jmcpheron/picowallet/pcb/dossier/review/design-SHA256SUMS.txt

81872eb326079a7e8b5d7d5e1b19cf433eb0403c9ab9667d025cbc219fbe951f  design/B_Cu.gbr
2e30690aaf0712d75476c412137e2d9d4d11c8428289b69405e05833194e1649  design/B_Fab.gbr
f35687d87080b0f3686ef03e0c079b65ae2d905b86f3cc0620ea2f5d0d830985  design/B_Mask.gbr
2a0583e4f1f08f04dc978bb757d1210283100e4770bd0bd72f40201c464b8a35  design/B_Paste.gbr
18354fdda90aefe86f01dbc70a8d4ac4ed9822576b9fddc27e66ef9b916f4a84  design/B_SilkScreen.gbr
823afdf04d9c6c309ea86c9f785da4fdbc58092ca9bf7bde5bf54fca331086fa  design/Edge_Cuts.gbr
74883b58e809d55b0bc6244c77d480d6ff0cdf29ce8e10337ea52f4309ef3243  design/F_Cu.gbr
3864f394b6c3a682efa8f601bc7bfb813e6d987ae6614617fa555495596dba0d  design/F_Fab.gbr
b160e3052a8e661215c279790700f99fbb2ffc0b1814cabcb3420a72b8e14e5f  design/F_Mask.gbr
32e1bcf6dd70280c164ed8c9ef9c4a6f6ab28e5e05525b5f646602e4656c239d  design/F_Paste.gbr
fa26761cb678f5d729ef340bc35bac94bdb7481baf55dc918cb9726121abf4fc  design/F_SilkScreen.gbr
e51e13ea9f5cf1a3aba80c6a51722b144459b42f5522a788d916678455eaf316  design/atecc.py
47671b0118b700f60f467894f0017c4a4e2a5c7ac43126a3a6d44d783a9fd7d2  design/bom.csv
d2cc3fe4df4a8d1846834ca9a9e89f41f807217c7fe938fec09531b38b37acd0  design/circuit.json
2ee32a19055a602a06975289f33ecc65a3ce496ac5d460f3bfe1b75e12f026f0  design/drill-L1-L2.drl
3384cc93c1c2be9ab5b2f0fb1482502fd087c7b10cccd2463c61746d04682a67  design/drill_npth.drl
8be491ffda8b9145977cb7c0e572acd9fb334808aeca49469461d0e41f01ffbe  design/imports/AFC42_S12FMA_1H.tsx
1a8972742a19d952bdef4a81dbc08a3eb12bbb6a474e405c41814c8e8f9f5cf7  design/imports/ATECC608B_SSHDA_T.tsx
1c11bdfb14c2074dd8337bcc206597ea0cd844397efaa37cbe0326824e9cc2fb  design/imports/A_2N7002K.tsx
b427f95c3ecb185a983220215d4f819d88e12597ac880b04713199add4100ca5  design/imports/B2B_PH_K_S_LF__SN_.tsx
0096762589c44025e8de1cc9b50725c5d652869b592f98cea48bb7ed34450979  design/imports/B8B_PH_K_S_LF__SN_.tsx
e7616fea44cbe588cf2a56cc619590fded075c63ccea7ce70d8436919f30bb55  design/imports/FPC_05FB_12PH20.tsx
7e6e95e033e55d2333b14894a894e1f6c5e5995f0d5044a608a69153240c5a7e  design/imports/HS20HS072RX.tsx
20b32934aec5f2864cbb48cf8da05da7b60f25d9f67b9723107a9162c68af262  design/imports/KH_6X6X5H_STM.tsx
8308a2bd2d0942416d6335a00306846be59e4fa2a5d607b795276ab017445468  design/imports/MCP2221A_I_ST.tsx
dc7c8d19167b896671e425b0ab83c15ee2b98f2e8f7ee3580d204d0af8f0a4de  design/imports/MSK12C02.tsx
080d922cc619edd11ae2b99730031f0dcc4e410ed6c89468a13a04f0ba893a95  design/imports/N114_2413THBIG01_H13.tsx
d8937ad016772eebd5f3176e59195f99bb56accab89966493c41f63082c26c04  design/imports/Raspberry_Pi_Pico_2W.tsx
e574e61f85b4c484d38929691d93fe90a69a7a41fd3f569a63147b37680dcbe7  design/imports/SKRHABE010.tsx
5de4d8bbd46f4217eb1491d092df8b797234da56ba7755f28d0653d1a24292b8  design/imports/SS14.tsx
67e55c82c61c12562ab0b4fbd8571564f8616f0f8f78ff265328f881599fb617  design/imports/TP4056.tsx
c4853684f1a7005c34f4000c8a4169bb6ec0265d493bd5304ac0a39d371ed727  design/imports/TYPE_C_24P_GTJB_040.tsx
a82b10c8e38ad41f17fd554e613dbc87036179dead6d384e9041da5c413de141  design/imports/TYPE_C_31_G_06.tsx
01b787781f85690d2ee1d6bc622a94667b03a3ae0d313eb4d7b8245be5163ab8  design/index.circuit.tsx
dd3722d458c4e9695f280ac042d3c78b1068ff26b8c834af29469a27c2366ffa  design/kicad-project.zip
5e905d84e344de93d0ba6c1a8fc089d557e6350b650668da4855b38a73cc6c2c  design/lcd.py
f00cfa05f2660cc76b7d9e6f8d97057246a0fbf60b70eb4c4683b0e3c232fc22  design/pick_and_place.csv
