jmcpheron/picowallet/pcb/dossier/NETLIST-v0.8.md

# Generated v0.8 netlist

Positions are compiled footprint centers, in mm. PCB rotations are not supplier CPL rotations.

| Part | X | Y | Side | PCB rotation |
|---|---:|---:|---|---:|
| U1 | -12.9400 | 0.0000 | bottom | 180 |
| DISP1 | 2.0000 | 0.0000 | top | 0 |
| J3 | -6.2500 | -0.4300 | top | 270 |
| C4 | -10.0000 | -6.0000 | top | 0 |
| R6 | 4.0000 | -20.5000 | top | 0 |
| Q1 | 10.0000 | -20.3000 | top | 0 |
| R7 | 9.0000 | -16.5000 | top | 0 |
| SW5 | -33.0000 | 0.0001 | top | 45 |
| SW1 | 34.0000 | 8.0000 | top | 90 |
| SW2 | 34.0000 | -6.0000 | top | 90 |
| U2 | -33.0000 | 15.0000 | top | 0 |
| R1 | -27.0000 | 19.0000 | top | 0 |
| R2 | -27.0000 | 11.0000 | top | 0 |
| C1 | -27.0000 | 15.0000 | top | 0 |
| BT1 | 28.0000 | 2.0000 | bottom | 0 |
| J2 | 28.0000 | 20.0000 | bottom | 0 |
| C2 | 24.0000 | -16.0000 | top | 0 |
| U3 | 30.0000 | -17.5000 | top | 0 |
| R3 | 35.5000 | -17.5000 | top | 90 |
| C3 | 24.0000 | -20.5000 | top | 0 |
| D1 | 18.0000 | -20.5000 | top | 0 |
| SW6 | -30.0000 | -19.2940 | top | 0 |
| SJ1 | 39.0000 | -10.0000 | top | 0 |
| R10 | 37.5000 | -14.0000 | top | 0 |
| Q2 | 18.0000 | -16.0000 | top | 0 |
| R8 | 13.0000 | -16.0000 | top | 0 |
| R9 | -23.0000 | -16.0000 | top | 0 |
| LED1 | -20.0000 | -20.0000 | top | 180 |
| R4 | -16.0000 | -20.0000 | top | 0 |
| LED2 | -8.0000 | -20.0000 | top | 180 |
| R5 | -4.0000 | -20.0000 | top | 0 |

## Connections

- unnamed / unconnected: U1.1
- unnamed / unconnected: U1.2
- GND: U1.3, U1.38, J3.1, J3.12, C4.2, Q1.2, R7.2, SW5.5, SW1.2, SW2.2, U2.4, C1.2, J2.2, C2.2, U3.1, U3.3, U3.9, R3.2, C3.2, SW6.3, R10.2, LED1.1
- unnamed / unconnected: U1.4, SW5.1
- unnamed / unconnected: U1.5, SW5.2
- SDA: U1.6, U2.5, R1.1
- SCL: U1.7, U2.6, R2.1
- unnamed / unconnected: U1.8
- unnamed / unconnected: U1.9
- unnamed / unconnected: U1.10
- unnamed / unconnected: U1.11, J3.3
- unnamed / unconnected: U1.12, J3.2
- unnamed / unconnected: U1.13
- unnamed / unconnected: U1.14, J3.4
- unnamed / unconnected: U1.15, J3.5
- unnamed / unconnected: U1.16, J3.6
- unnamed / unconnected: U1.17, Q1.1, R7.1
- unnamed / unconnected: U1.18
- unnamed / unconnected: U1.19
- unnamed / unconnected: U1.20, SW1.1
- unnamed / unconnected: U1.21, SW5.3
- unnamed / unconnected: U1.22, SW2.1
- unnamed / unconnected: U1.23
- unnamed / unconnected: U1.24, SW5.6
- unnamed / unconnected: U1.25
- unnamed / unconnected: U1.26, SW5.4
- unnamed / unconnected: U1.27
- unnamed / unconnected: U1.28
- unnamed / unconnected: U1.29
- unnamed / unconnected: U1.30
- unnamed / unconnected: U1.31
- unnamed / unconnected: U1.32
- unnamed / unconnected: U1.33
- unnamed / unconnected: U1.34
- unnamed / unconnected: U1.35
- V3_3: U1.36, J3.8, J3.9, C4.1, U2.8, R1.2, R2.2, C1.1, R4.1
- unnamed / unconnected: U1.37
- VSYS: U1.39, R6.1, D1.1
- VBUS: U1.40, C2.1, U3.4, SJ1.1, R5.1
- unnamed / unconnected: U1.41
- unnamed / unconnected: U1.42
- unnamed / unconnected: U1.43
- unnamed / unconnected: U1.44
- unnamed / unconnected: U1.45
- unnamed / unconnected: U1.46
- unnamed / unconnected: DISP1.1
- unnamed / unconnected: J3.7
- unnamed / unconnected: J3.10, R6.2
- unnamed / unconnected: J3.11, Q1.3
- unnamed / unconnected: J3.13
- unnamed / unconnected: J3.14
- unnamed / unconnected: SW5.7
- unnamed / unconnected: SW5.8
- unnamed / unconnected: SW1.3
- unnamed / unconnected: SW1.4
- unnamed / unconnected: SW2.3
- unnamed / unconnected: SW2.4
- unnamed / unconnected: U2.1
- unnamed / unconnected: U2.2
- unnamed / unconnected: U2.3
- unnamed / unconnected: U2.7
- unnamed / unconnected: BT1.1
- BAT: J2.1, U3.5, C3.1, SW6.1, Q2.2, R8.1
- unnamed / unconnected: U3.2, R3.1
- unnamed / unconnected: U3.6
- unnamed / unconnected: U3.7, LED2.2
- unnamed / unconnected: U3.8, SJ1.2, R10.1
- unnamed / unconnected: D1.2, Q2.3
- unnamed / unconnected: SW6.2, R9.1
- unnamed / unconnected: SW6.4
- unnamed / unconnected: SW6.5
- unnamed / unconnected: SW6.6
- unnamed / unconnected: SW6.7
- unnamed / unconnected: Q2.1, R8.2, R9.2
- unnamed / unconnected: LED1.2, R4.2
- unnamed / unconnected: LED2.1, R5.2

## J3 pads

| Pin | X | Y |
|---|---:|---:|
| 1 | -5.0000 | 2.3200 |
| 2 | -5.0000 | 1.8200 |
| 3 | -5.0000 | 1.3200 |
| 4 | -5.0000 | 0.8200 |
| 5 | -5.0000 | 0.3200 |
| 6 | -5.0000 | -0.1800 |
| 7 | -5.0000 | -0.6800 |
| 8 | -5.0000 | -1.1800 |
| 9 | -5.0000 | -1.6800 |
| 10 | -5.0000 | -2.1800 |
| 11 | -5.0000 | -2.6800 |
| 12 | -5.0000 | -3.1800 |
| 13 | -7.5000 | -4.1800 |
| 14 | -7.5000 | 3.3200 |
