jmcpheron/picowallet/art/bar_screen.png

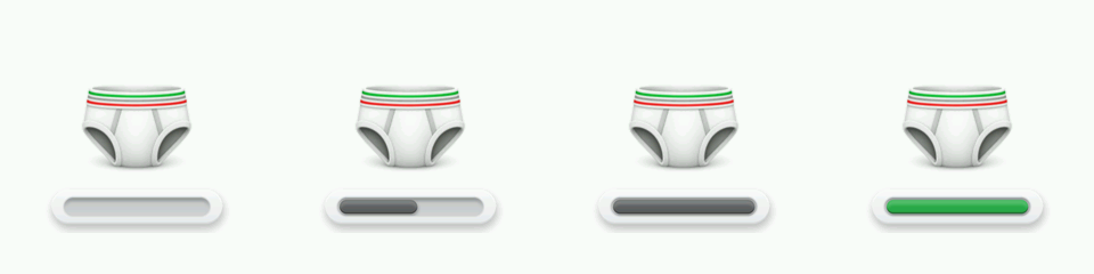
art/bar_screen.png
