jmcpheron/picowallet/case/zez0000/base_v5_qr_bottom.png

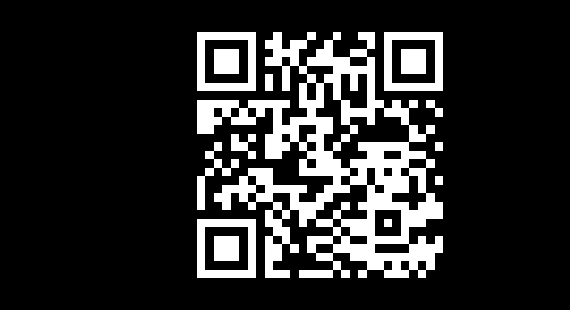
case/zez0000/base_v5_qr_bottom.png
