jmcpheron/picowallet/g3.png

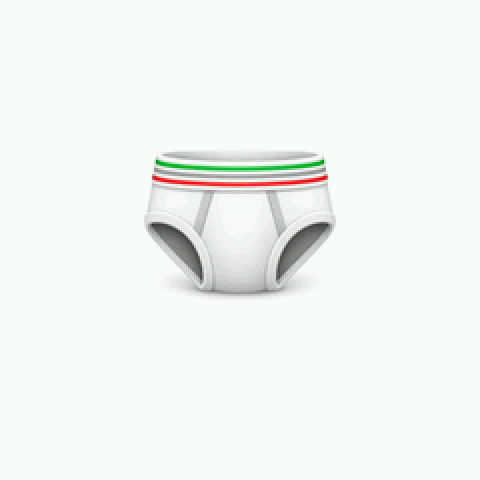
g3.png
