jmcpheron/picowallet/pcb/dossier/datasheets/panel-page-01.png

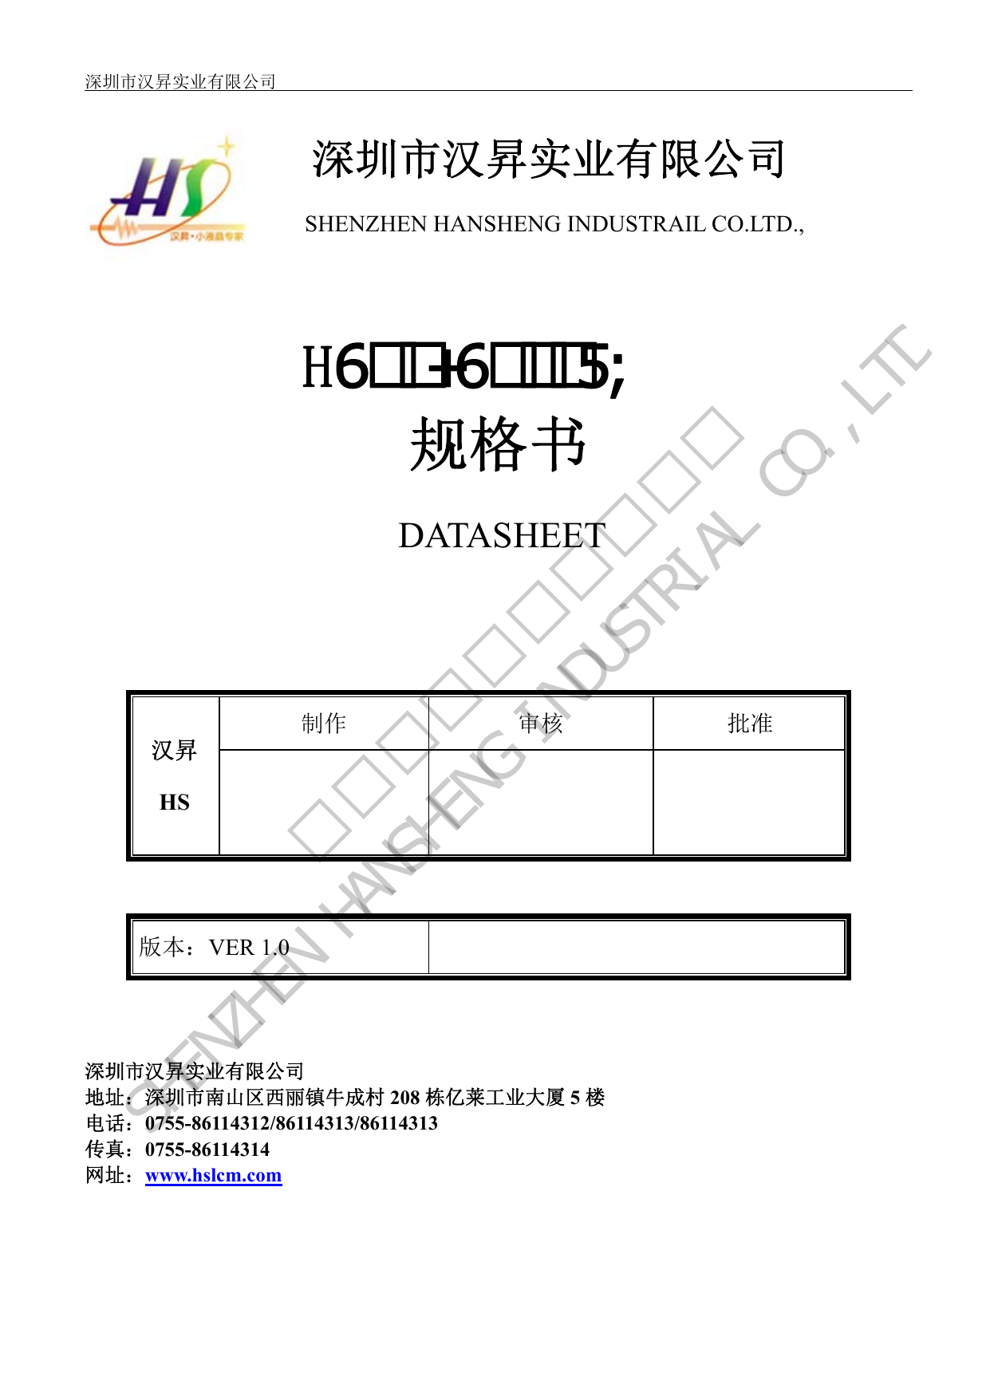
pcb/dossier/datasheets/panel-page-01.png
