jmcpheron/picowallet/pcb/dossier/datasheets/panel-page-02.png

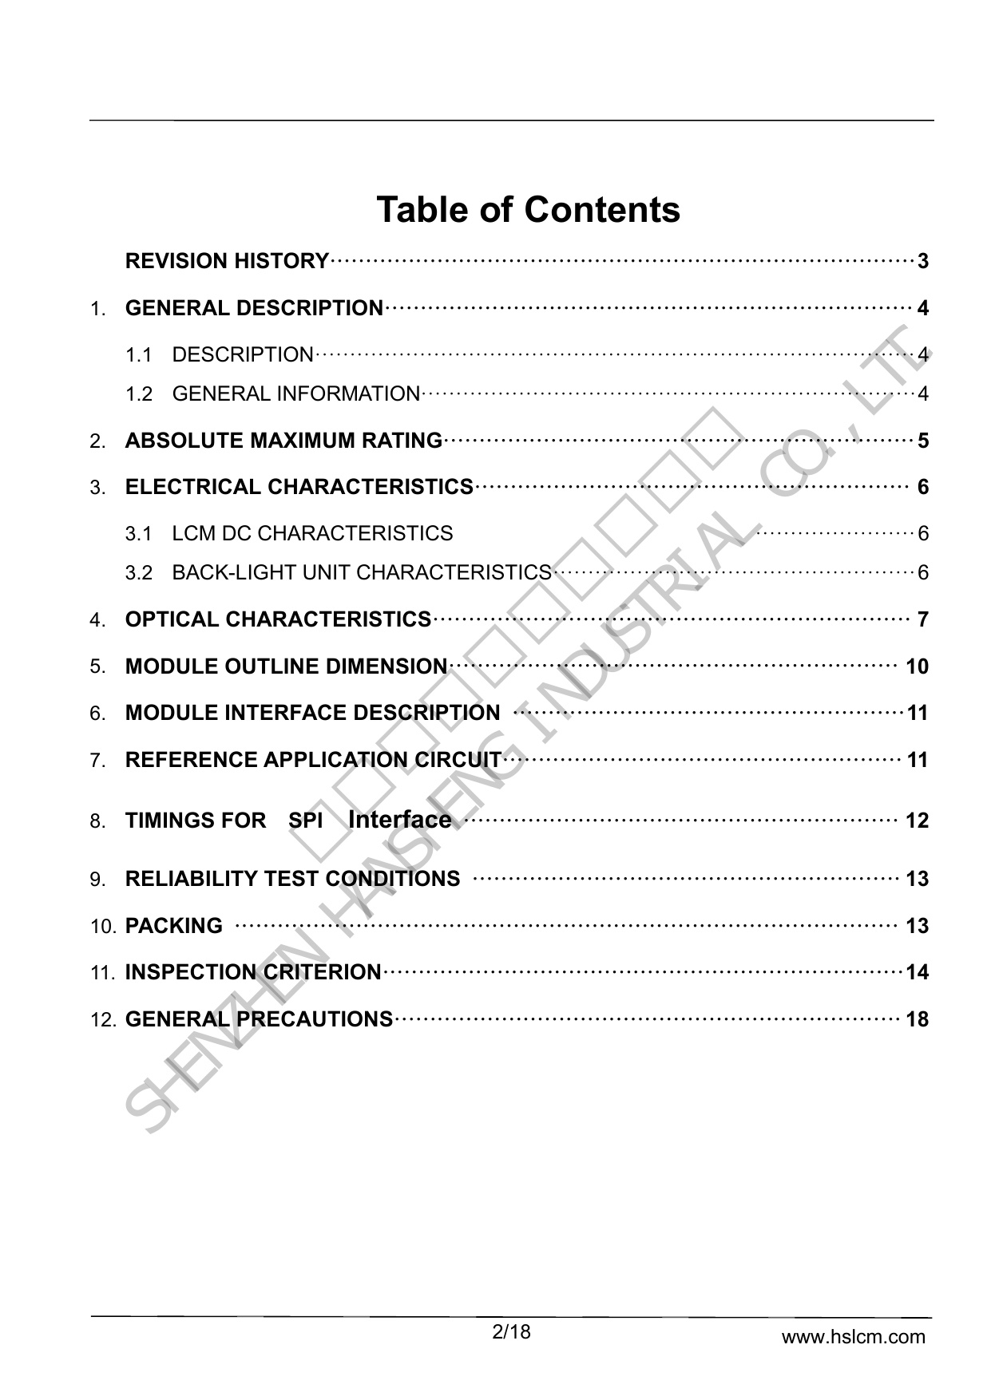
pcb/dossier/datasheets/panel-page-02.png
