jmcpheron/picowallet/pcb/dossier/datasheets/panel-page-03.png

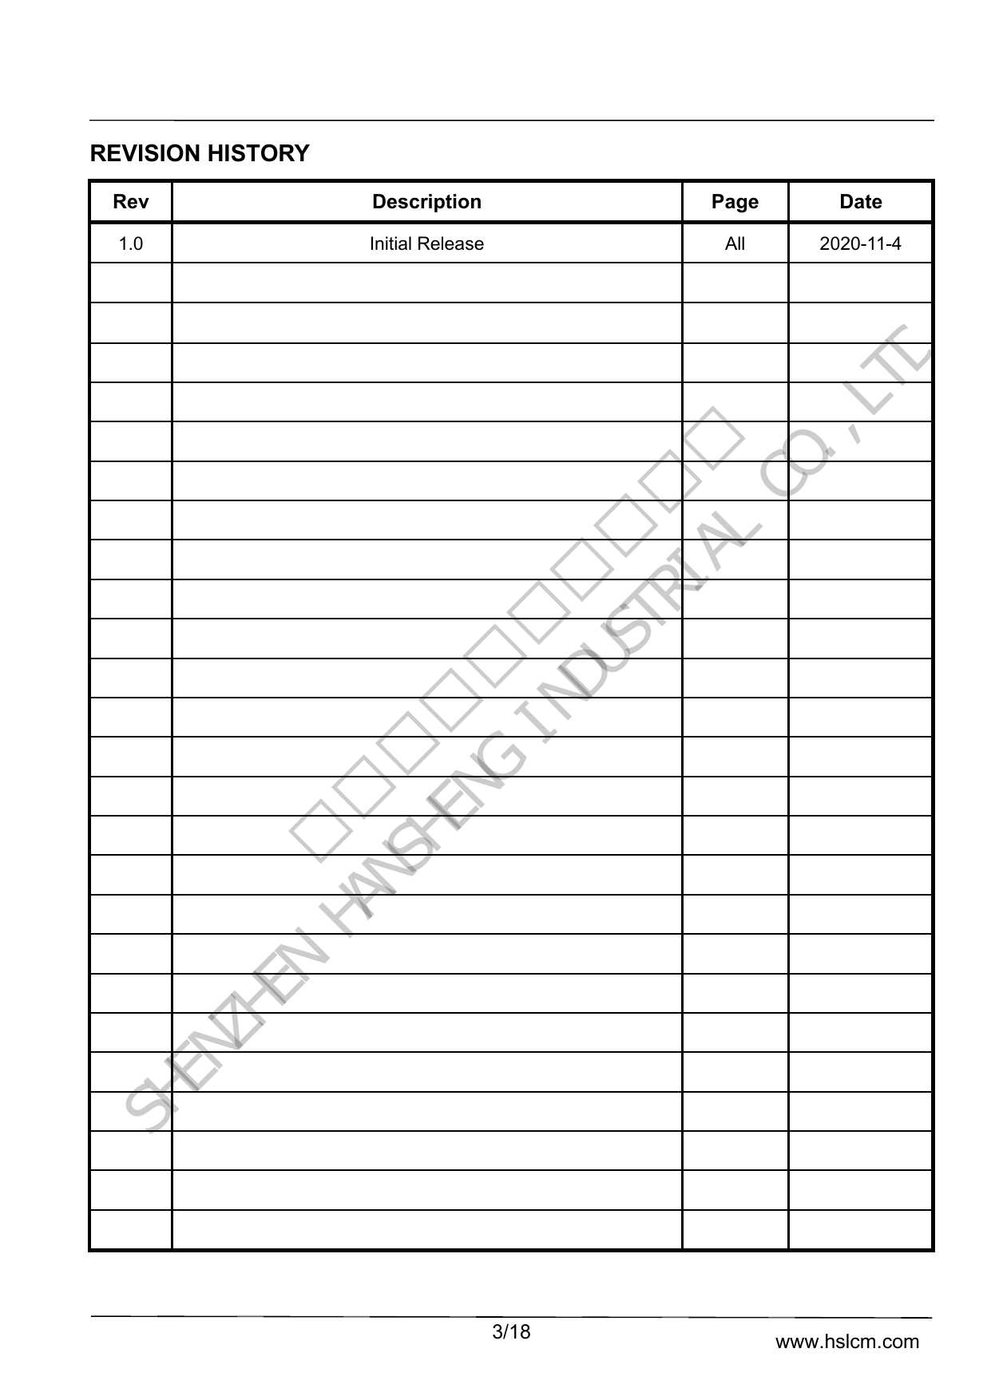
pcb/dossier/datasheets/panel-page-03.png
