jmcpheron/picowallet/pcb/dossier/datasheets/panel-page-04.png

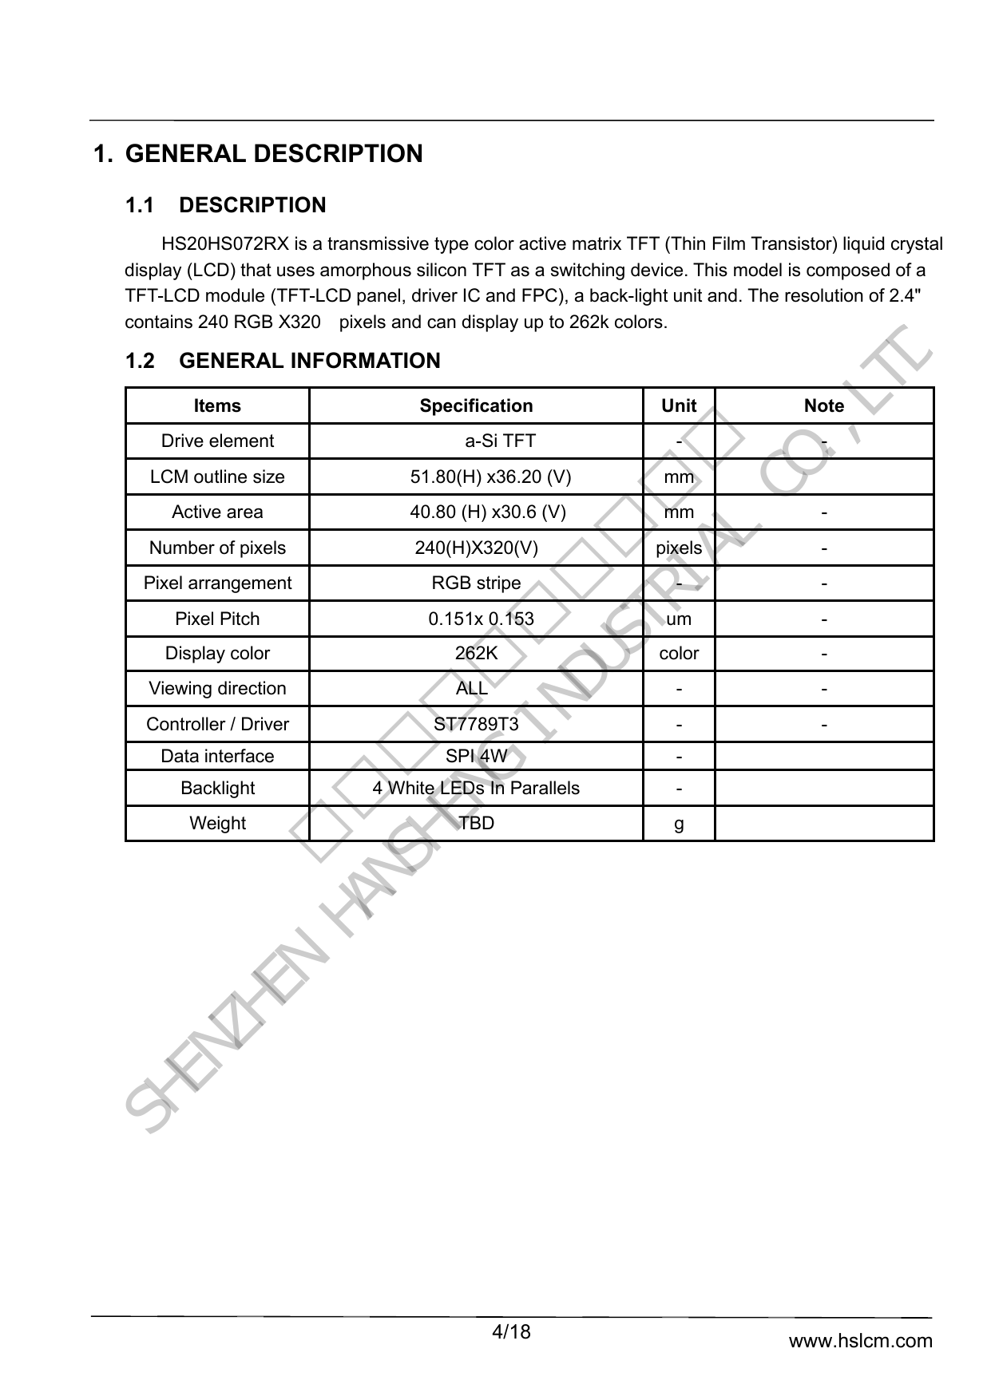
pcb/dossier/datasheets/panel-page-04.png
