jmcpheron/picowallet/pcb/dossier/datasheets/panel-page-05.png

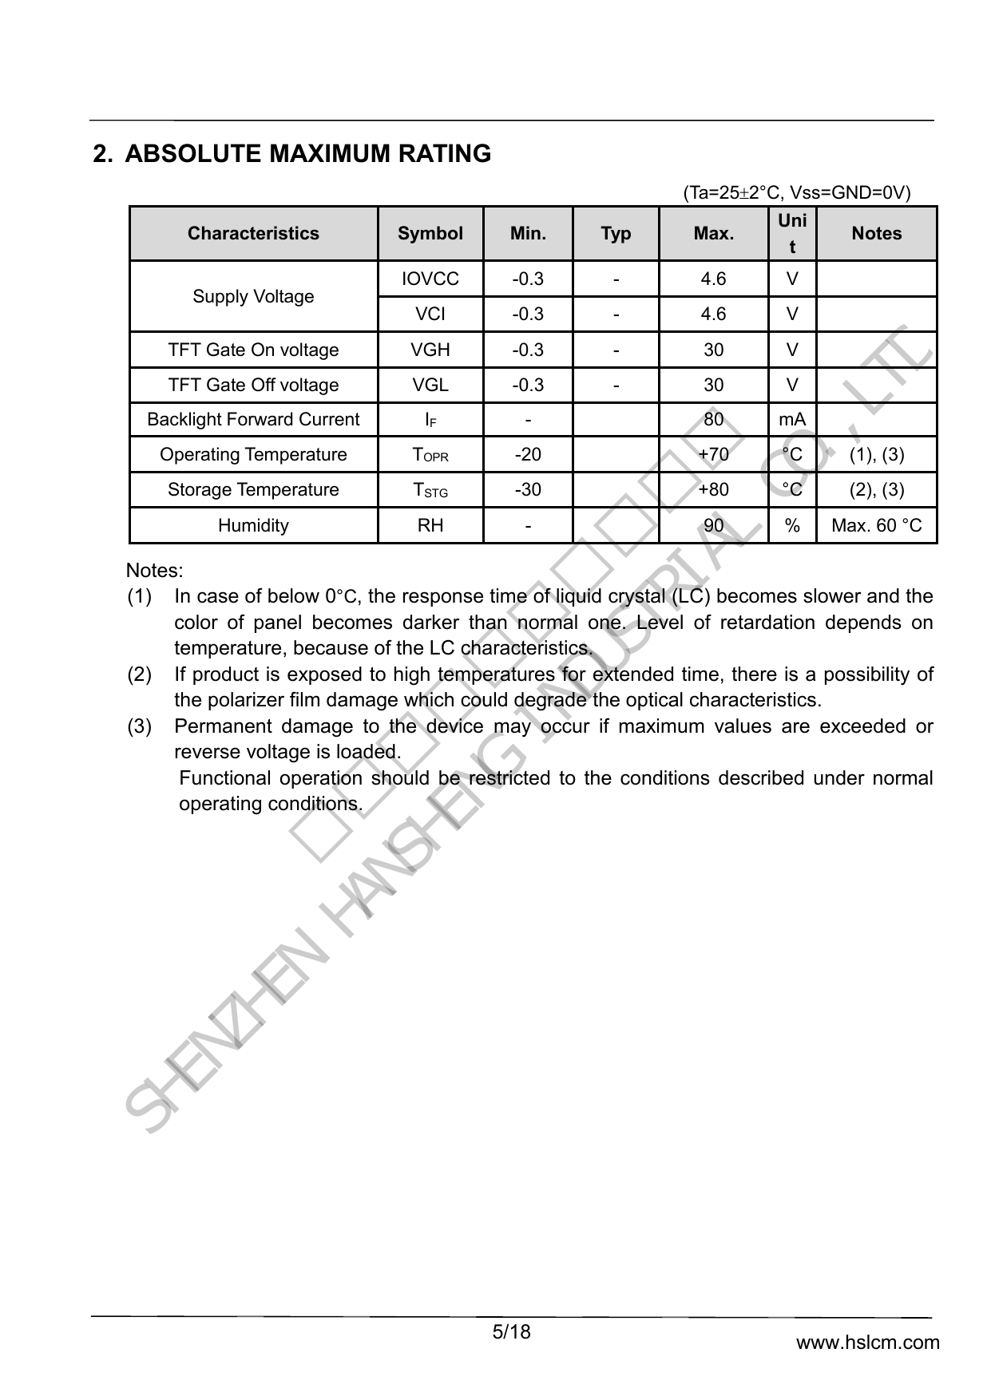
pcb/dossier/datasheets/panel-page-05.png
