jmcpheron/picowallet/pcb/dossier/datasheets/panel-page-06.png

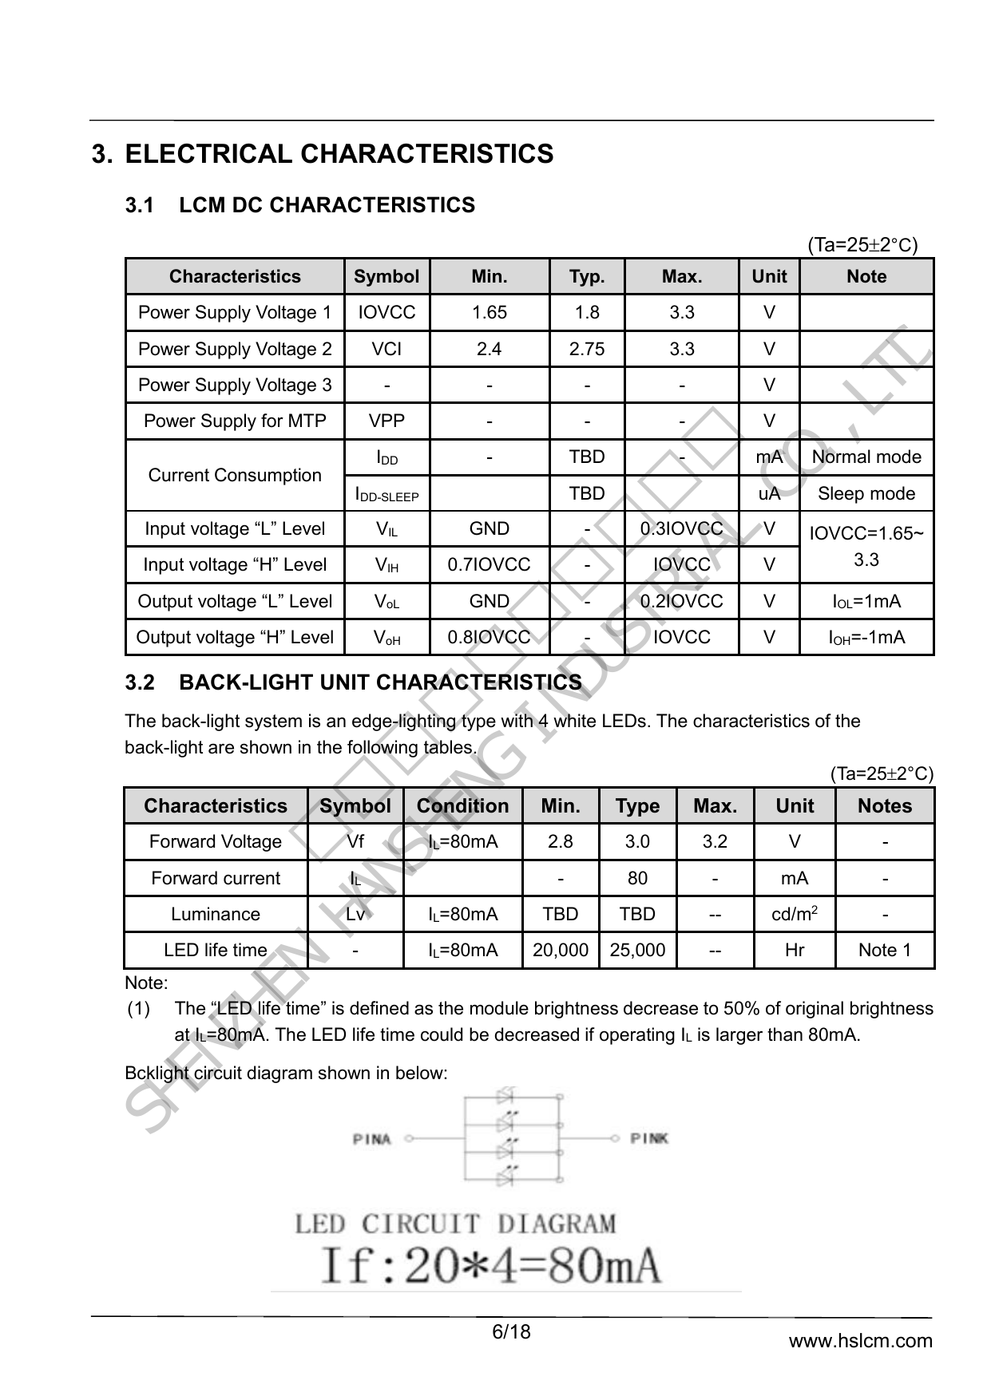
pcb/dossier/datasheets/panel-page-06.png
