jmcpheron/picowallet/pcb/dossier/datasheets/panel-page-07.png

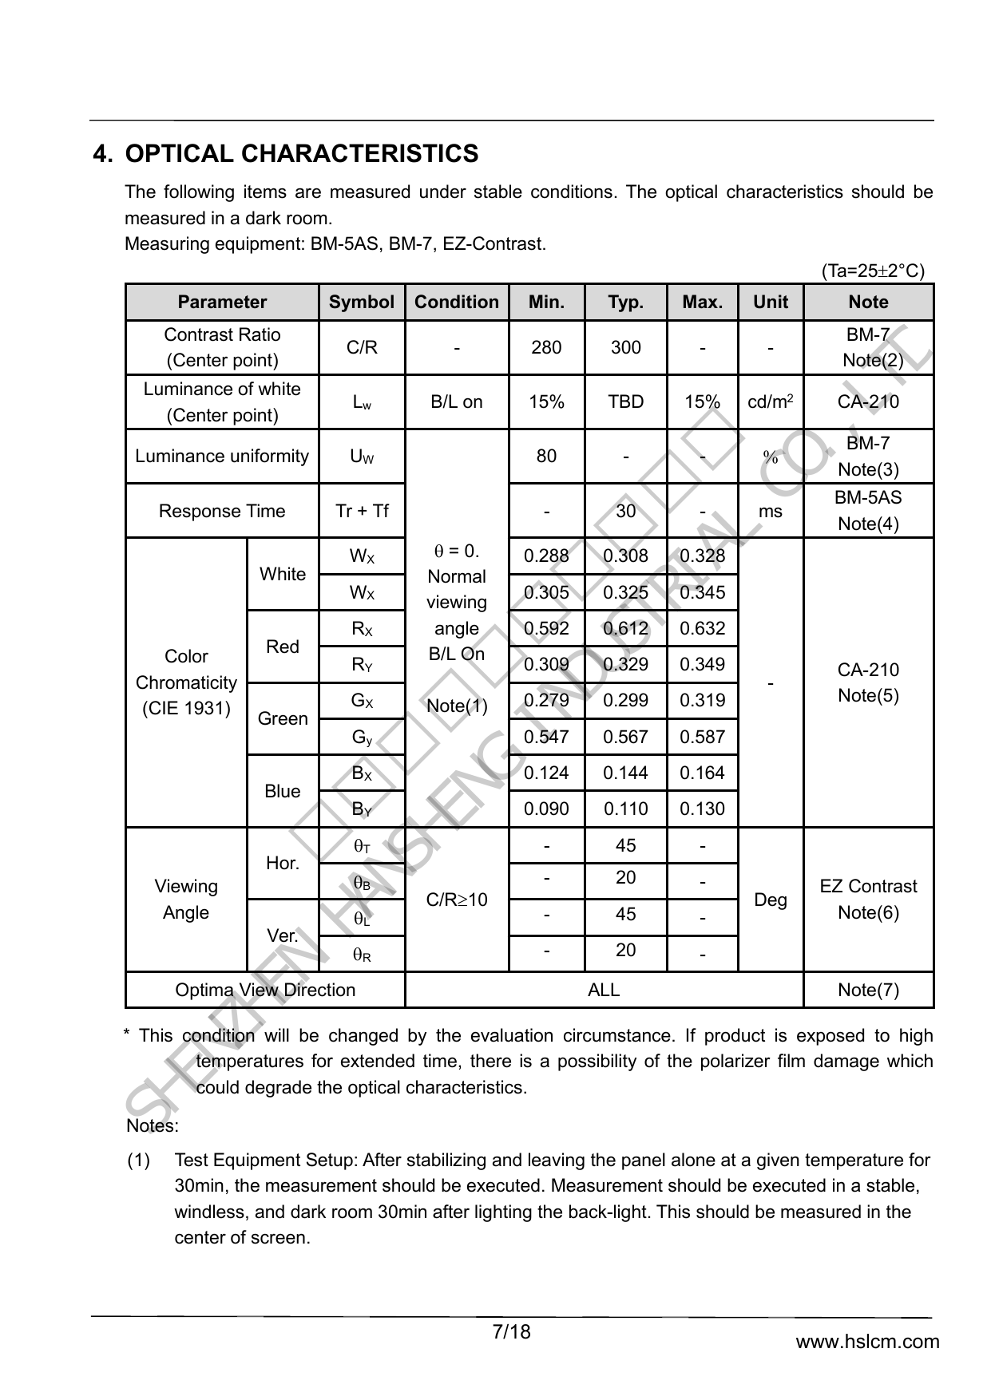
pcb/dossier/datasheets/panel-page-07.png
