jmcpheron/picowallet/pcb/dossier/datasheets/panel-page-08.png

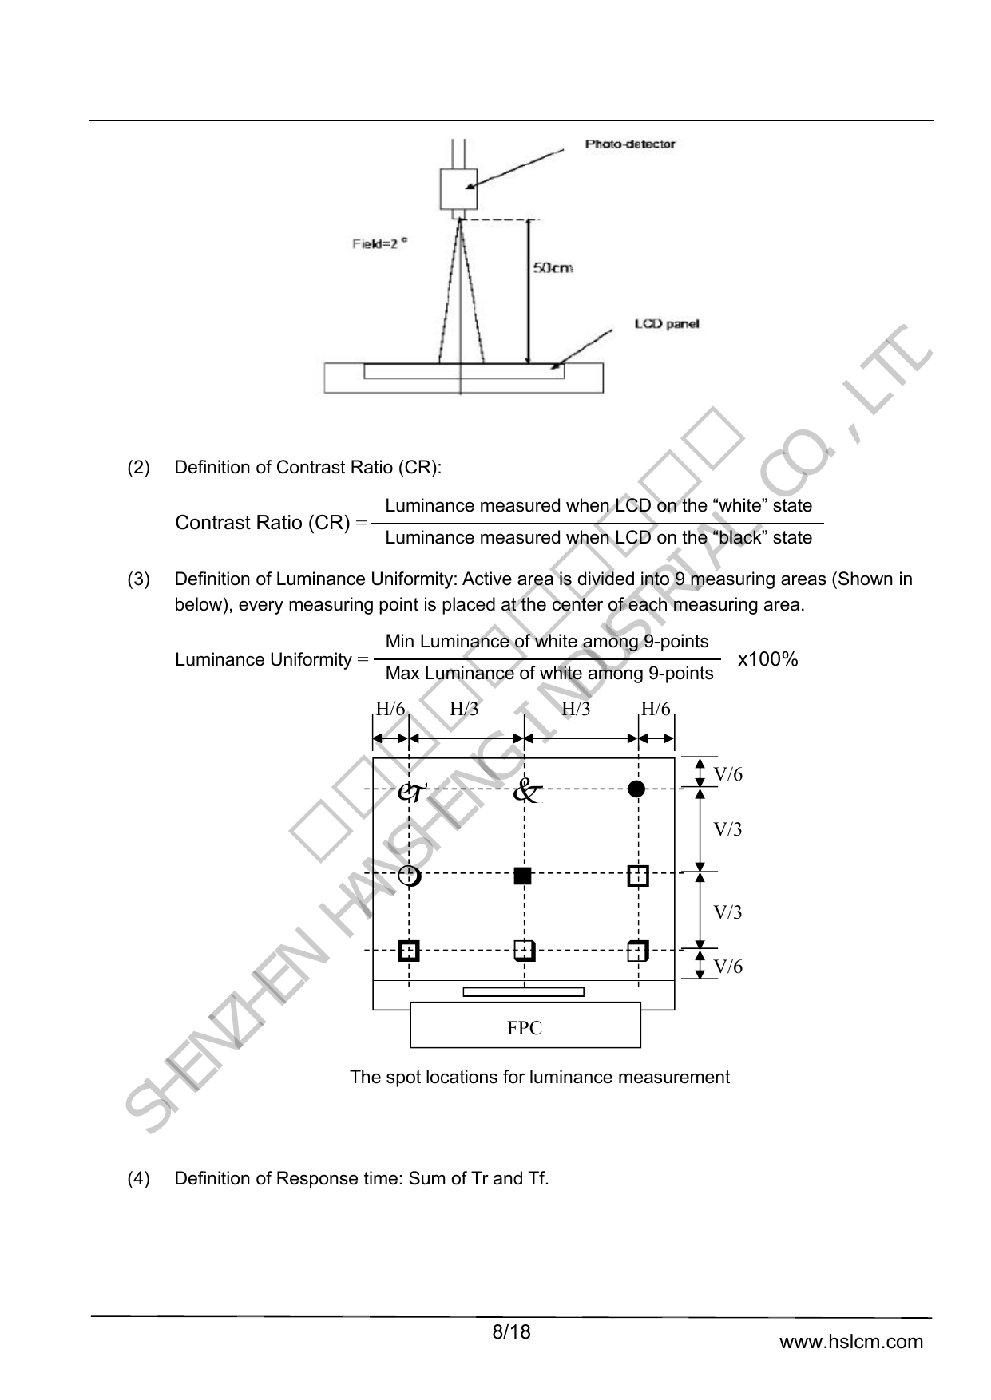
pcb/dossier/datasheets/panel-page-08.png
