jmcpheron/picowallet/pcb/dossier/datasheets/panel-page-09.png

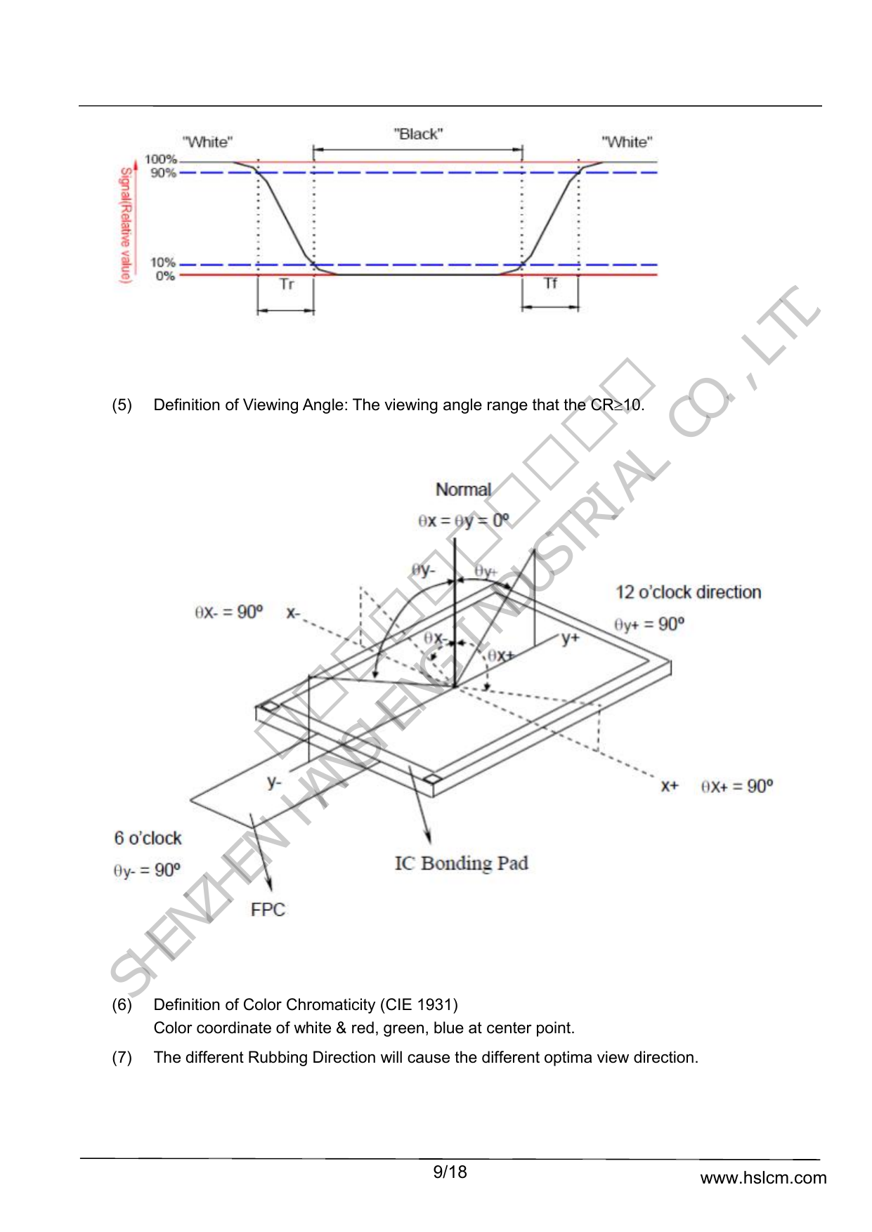
pcb/dossier/datasheets/panel-page-09.png
