jmcpheron/picowallet/pcb/dossier/datasheets/panel-page-10.png

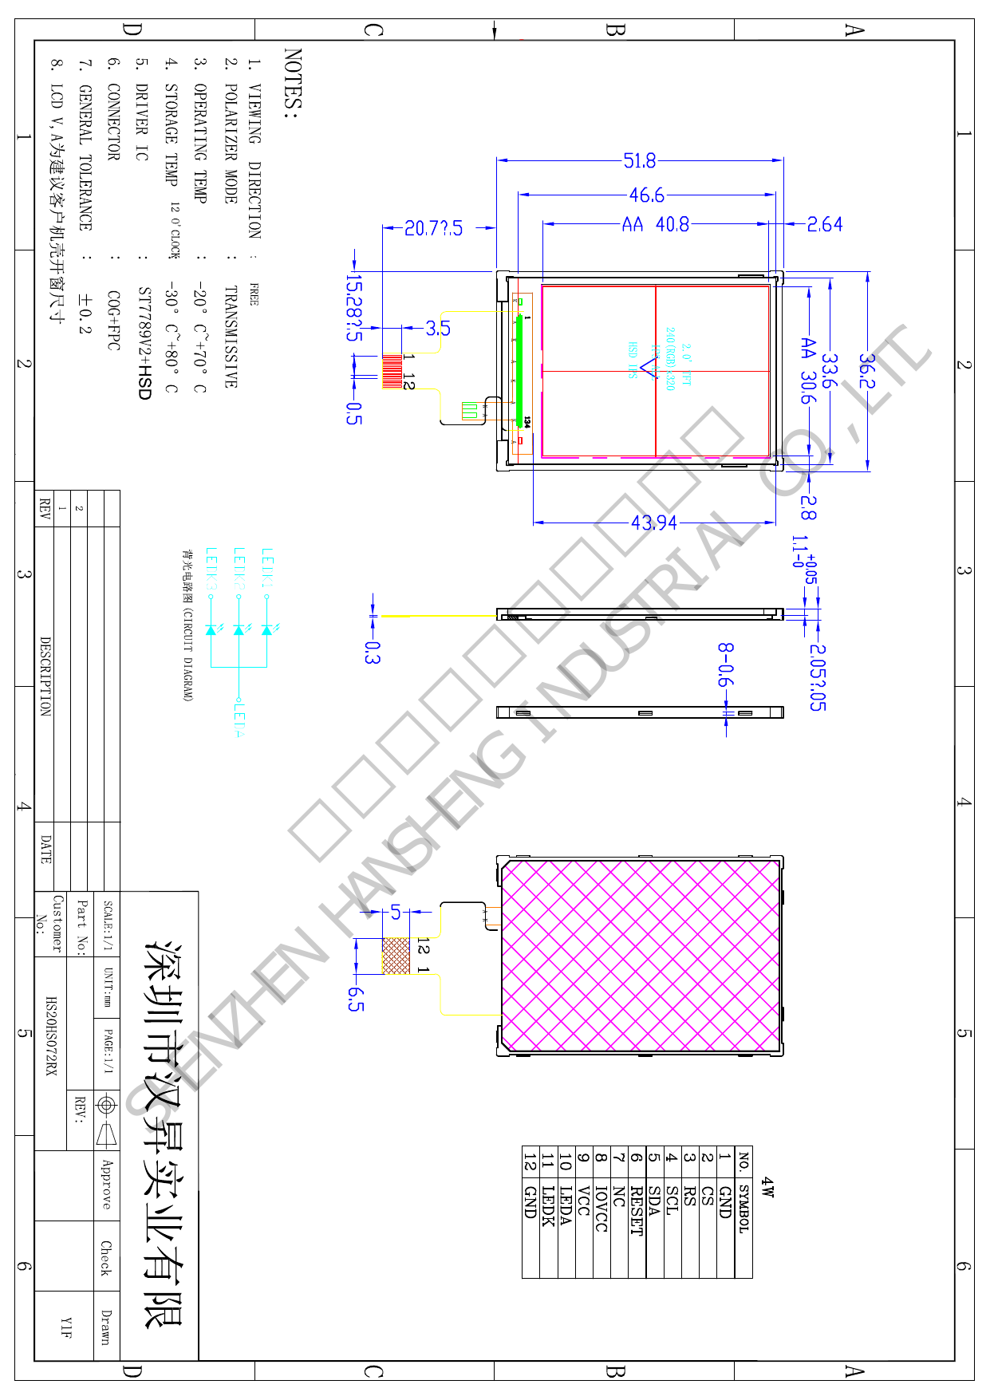
pcb/dossier/datasheets/panel-page-10.png
