jmcpheron/picowallet/pcb/dossier/datasheets/panel-page-11.png

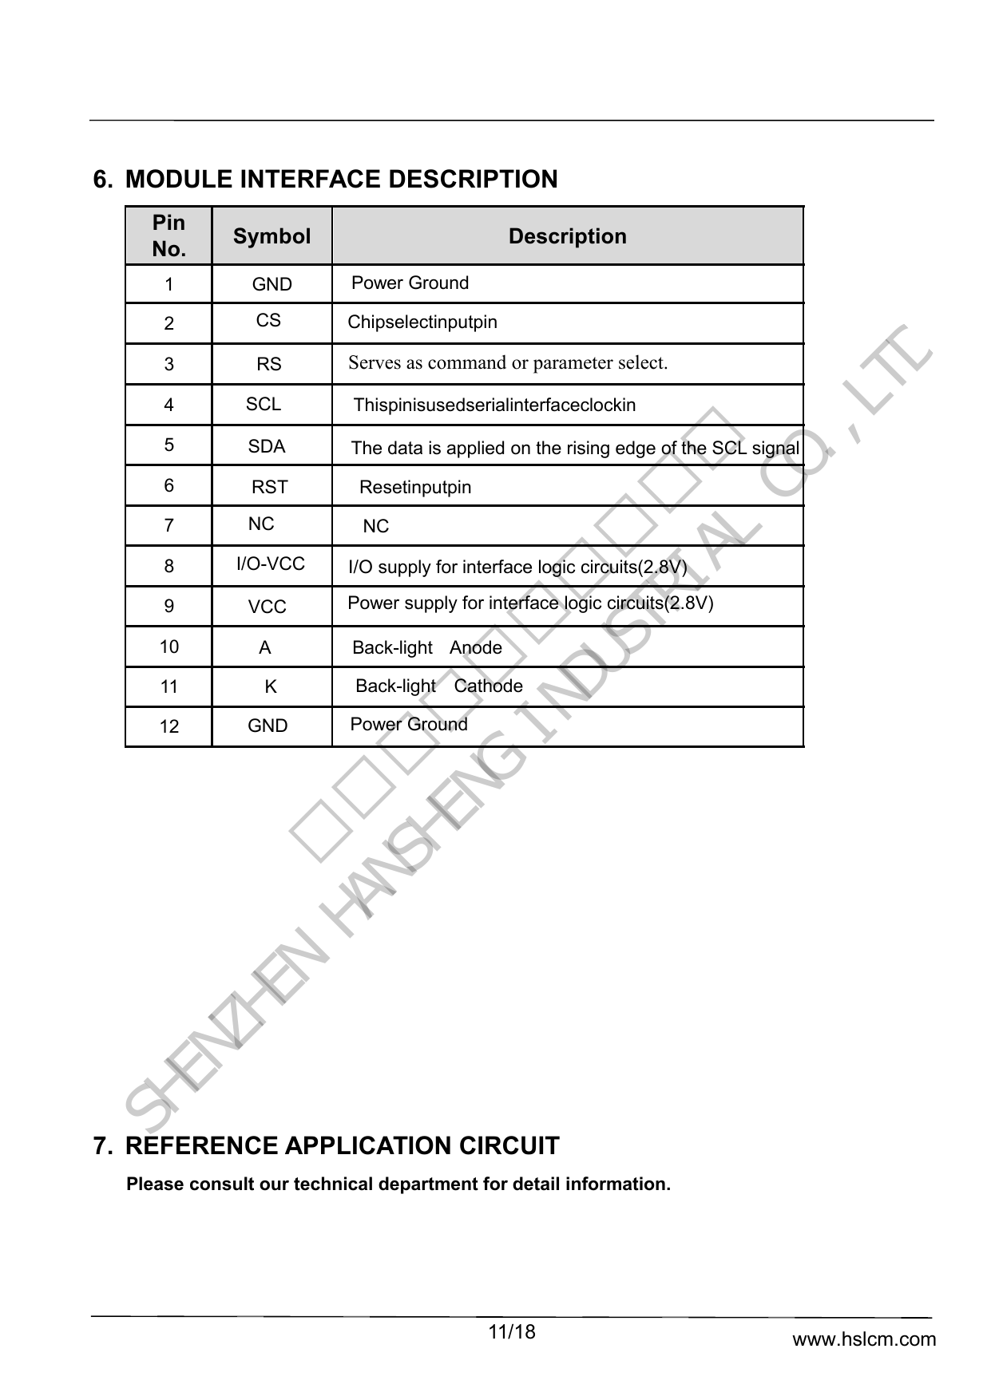
pcb/dossier/datasheets/panel-page-11.png
