jmcpheron/picowallet/pcb/dossier/datasheets/panel-page-12.png

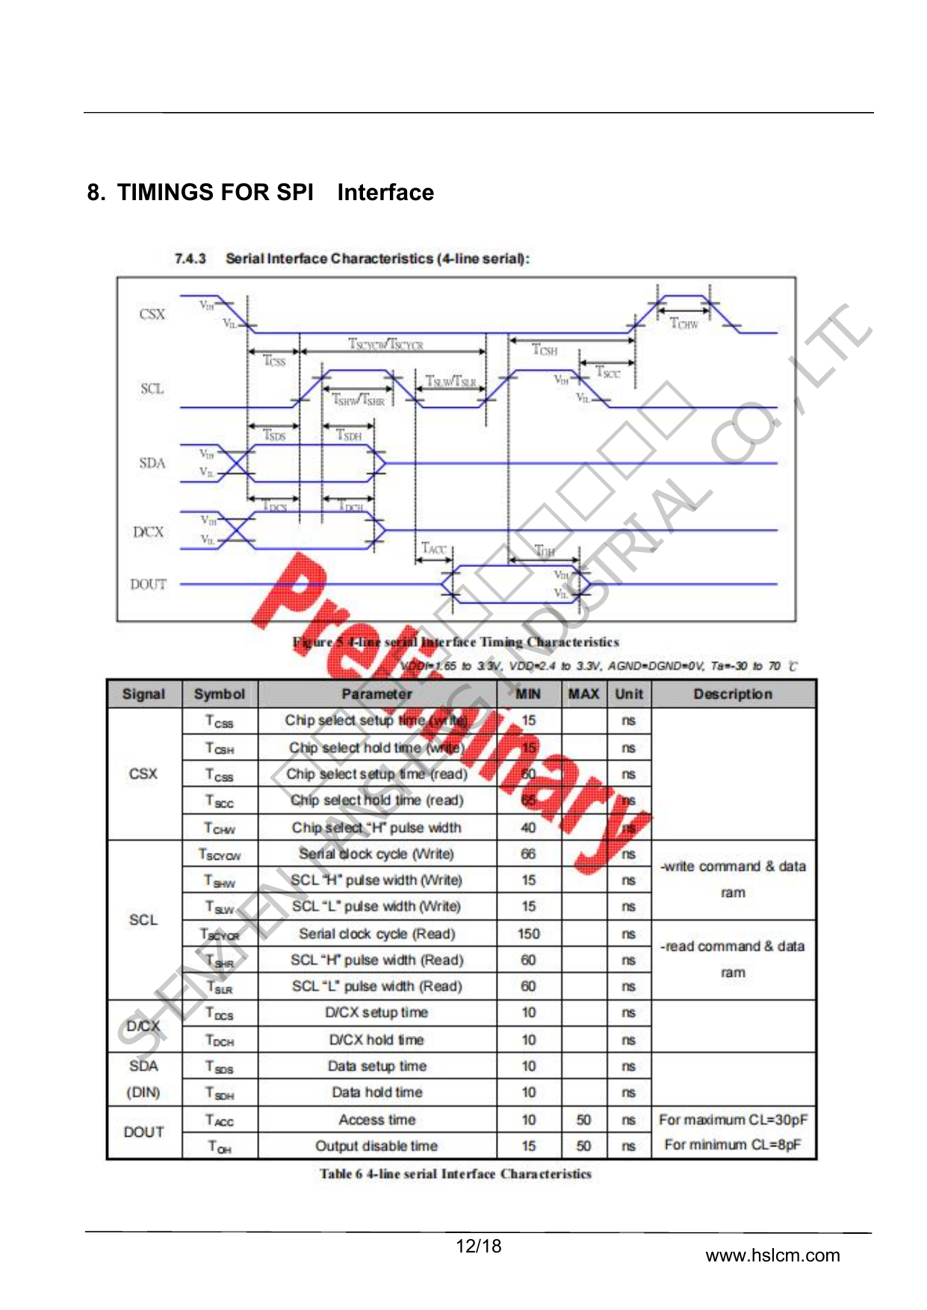
pcb/dossier/datasheets/panel-page-12.png
