jmcpheron/picowallet/pcb/dossier/datasheets/panel-page-13.png

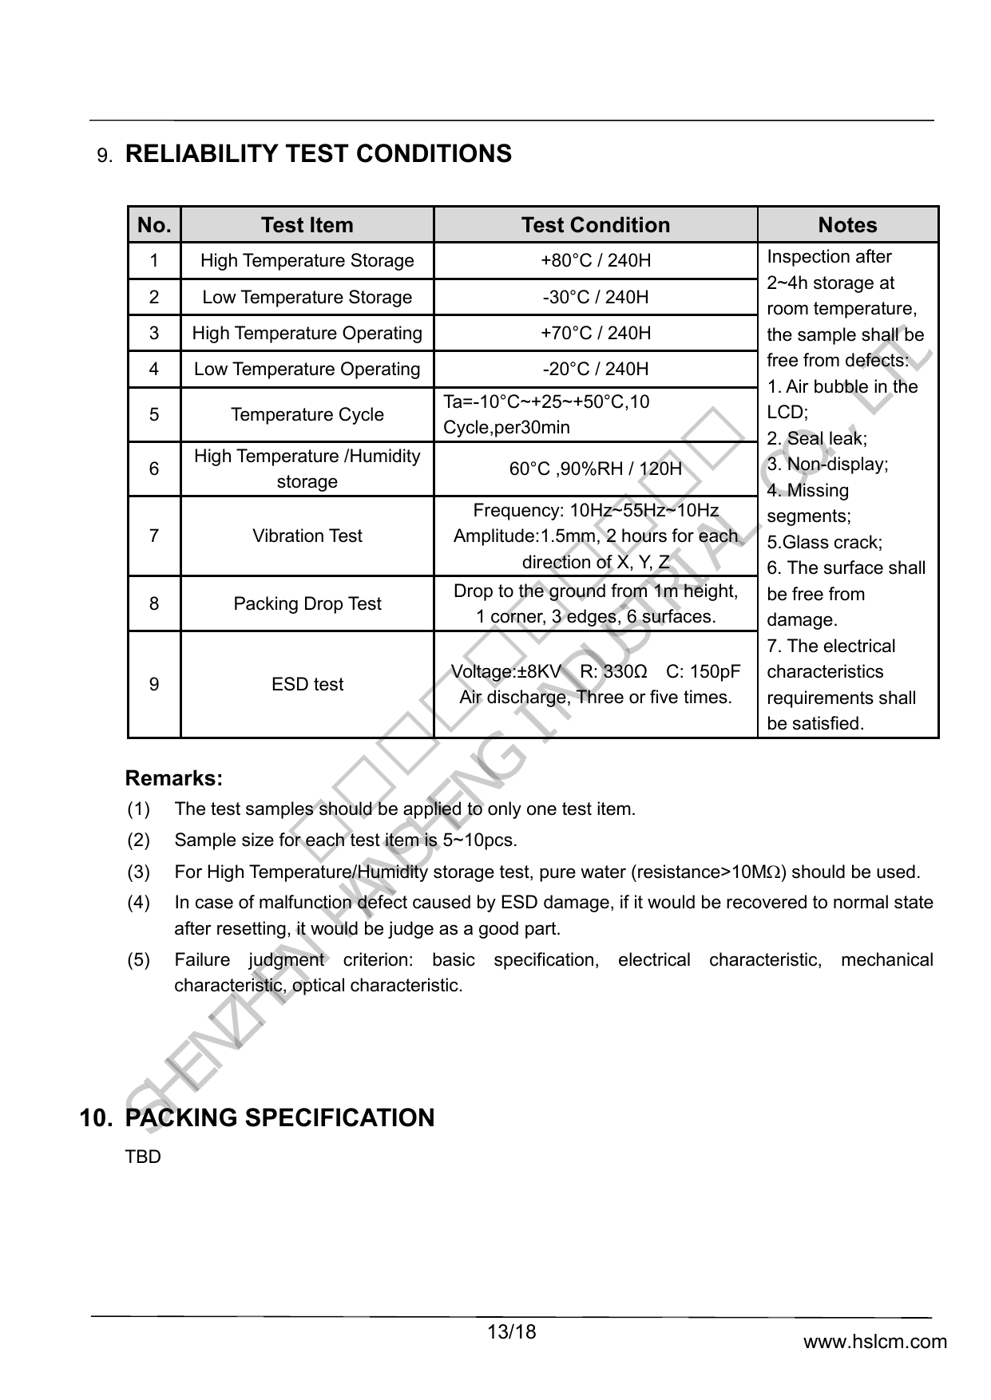
pcb/dossier/datasheets/panel-page-13.png
