jmcpheron/picowallet/pcb/dossier/datasheets/panel-page-14.png

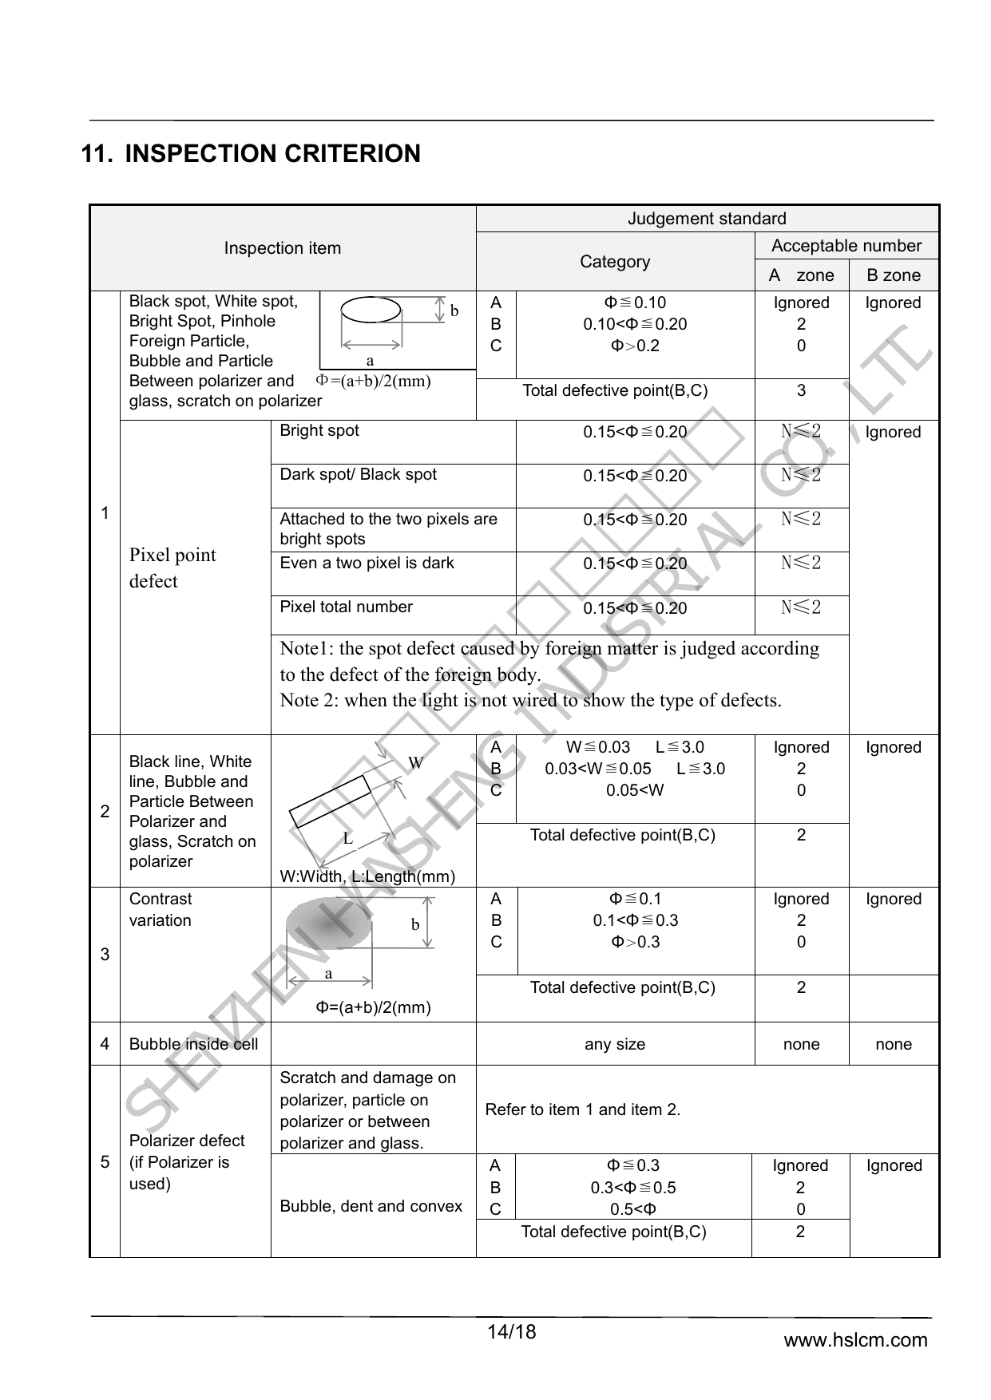
pcb/dossier/datasheets/panel-page-14.png
