jmcpheron/picowallet/pcb/dossier/datasheets/panel-page-15.png

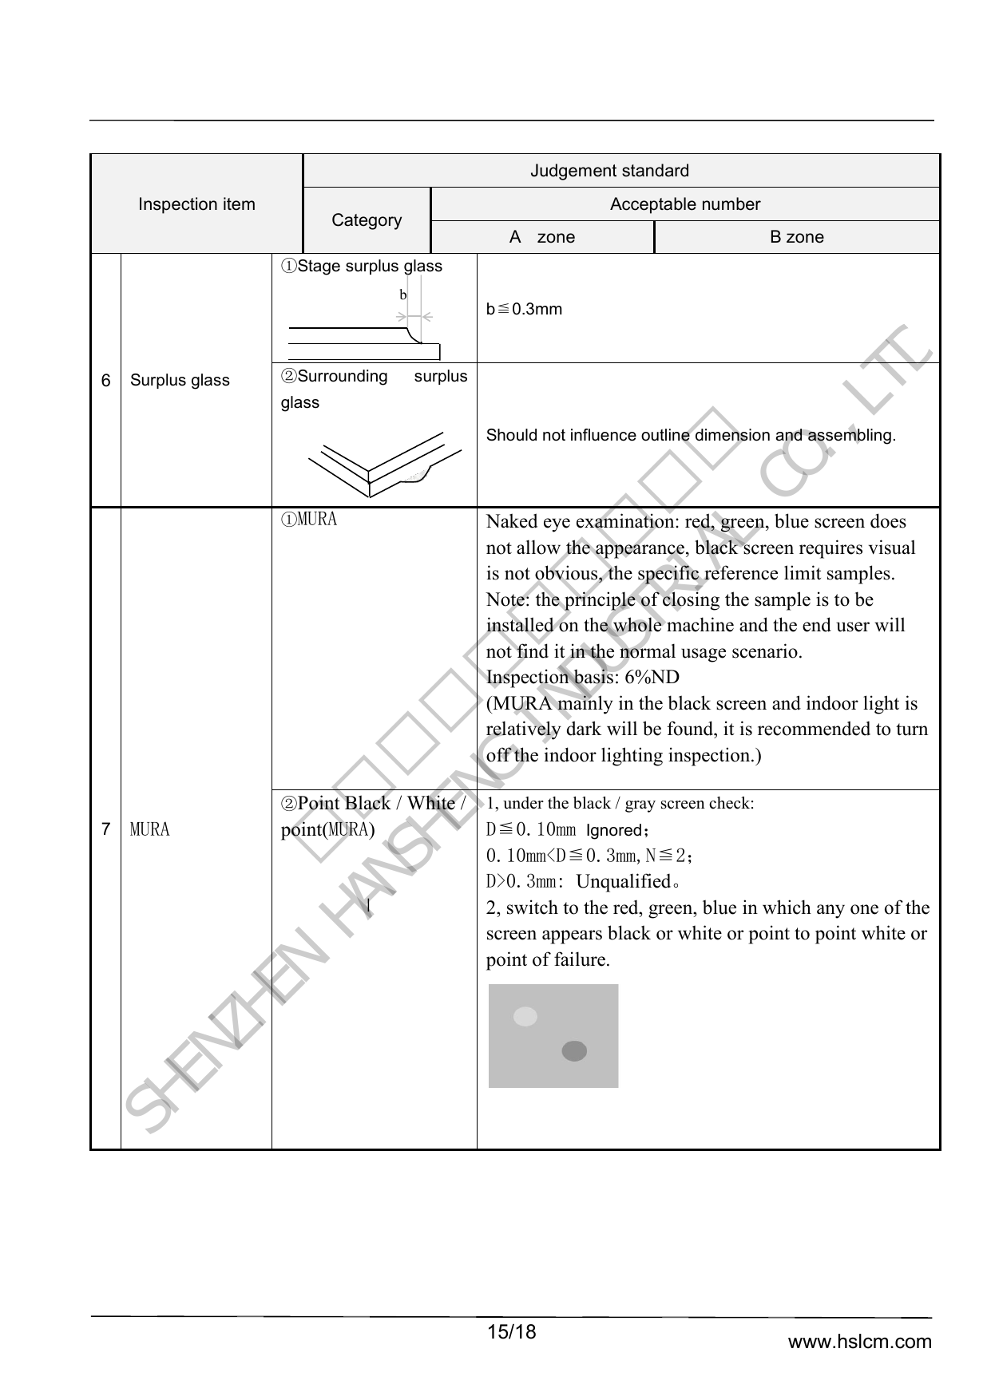
pcb/dossier/datasheets/panel-page-15.png
