jmcpheron/picowallet/pcb/dossier/img/3d-top.png

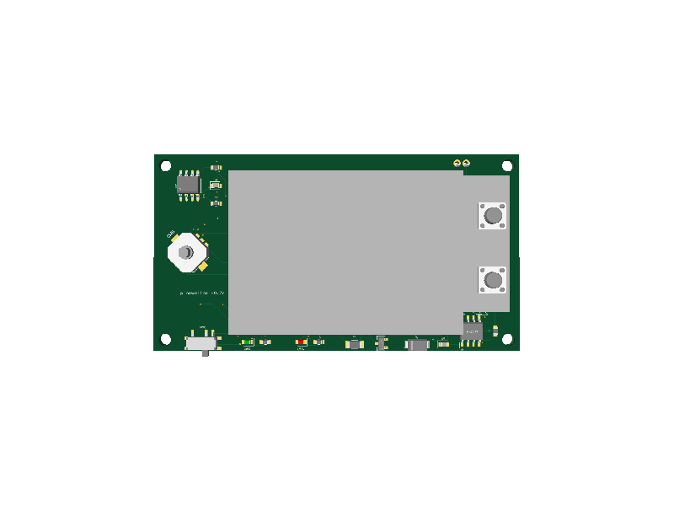
pcb/dossier/img/3d-top.png
