jmcpheron/picowallet/pcb/dossier/img/3d.png

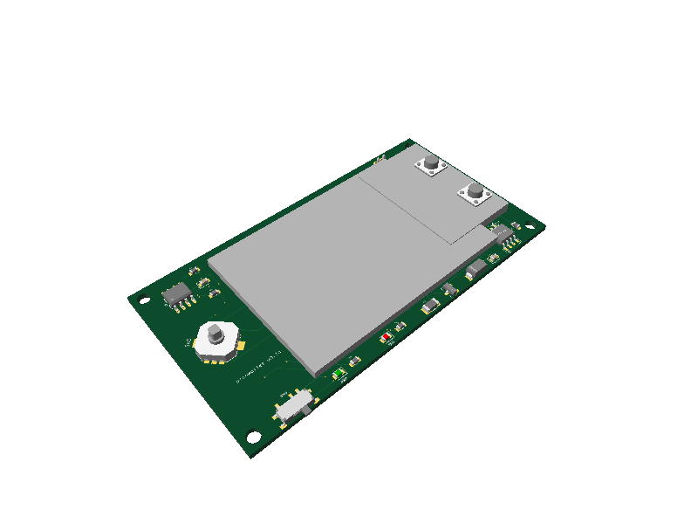
pcb/dossier/img/3d.png
