jmcpheron/picowallet/pcb/dossier/img/copper-latch-region.png

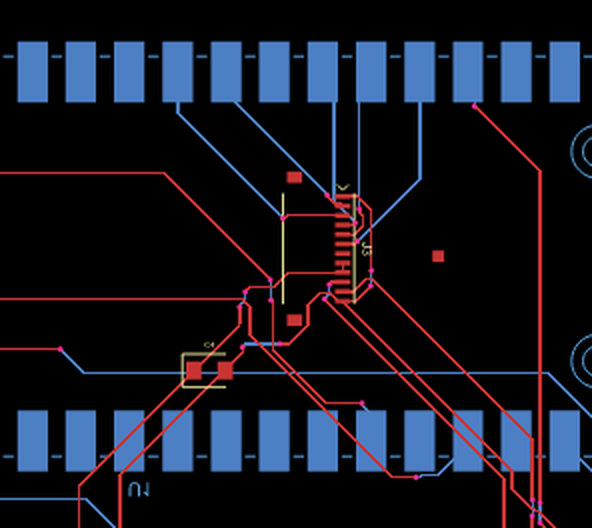
pcb/dossier/img/copper-latch-region.png
