jmcpheron/picowallet/pcb/dossier/img/copper.png

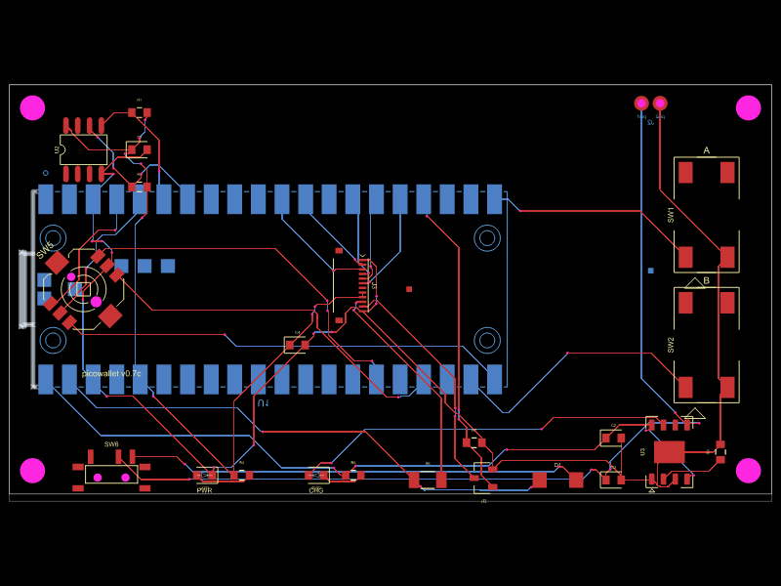
pcb/dossier/img/copper.png
