jmcpheron/picowallet/pcb/dossier/img/jlcpcb-part-photos/jlcpcb-placement-v07c-1.png

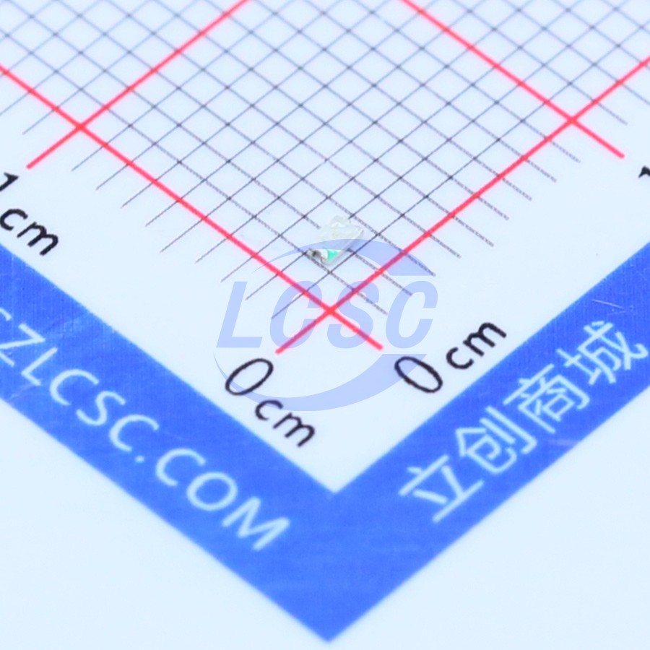
pcb/dossier/img/jlcpcb-part-photos/jlcpcb-placement-v07c-1.png
