jmcpheron/picowallet/pcb/dossier/img/jlcpcb-part-photos/jlcpcb-placement-v07c-5.png

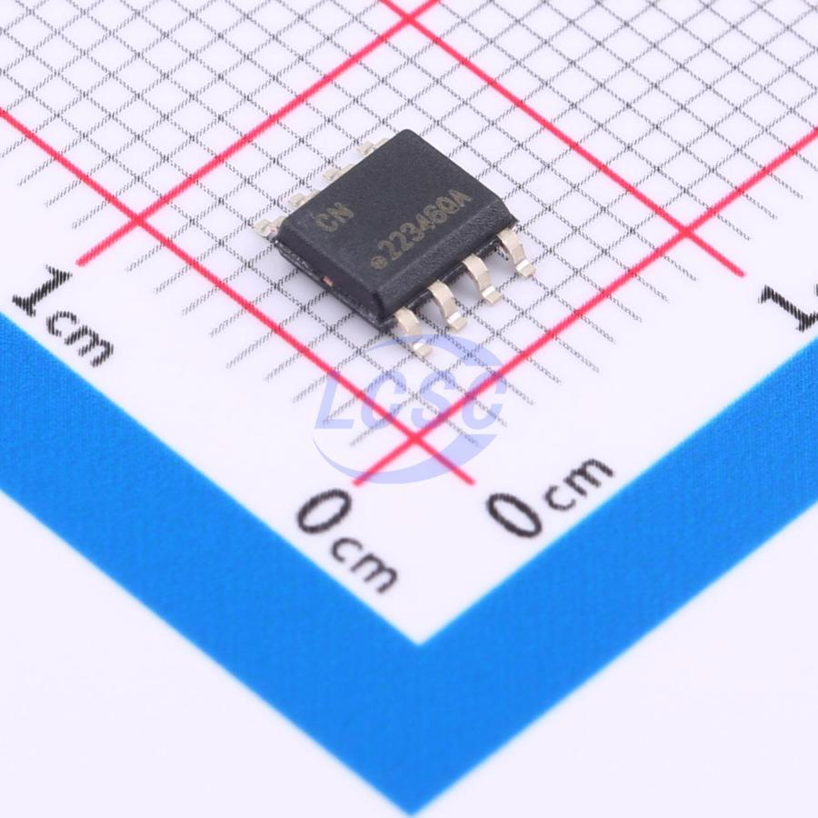
pcb/dossier/img/jlcpcb-part-photos/jlcpcb-placement-v07c-5.png
