jmcpheron/picowallet/pcb/dossier/img/jlcpcb-part-photos/jlcpcb-placement-v07c-10.png

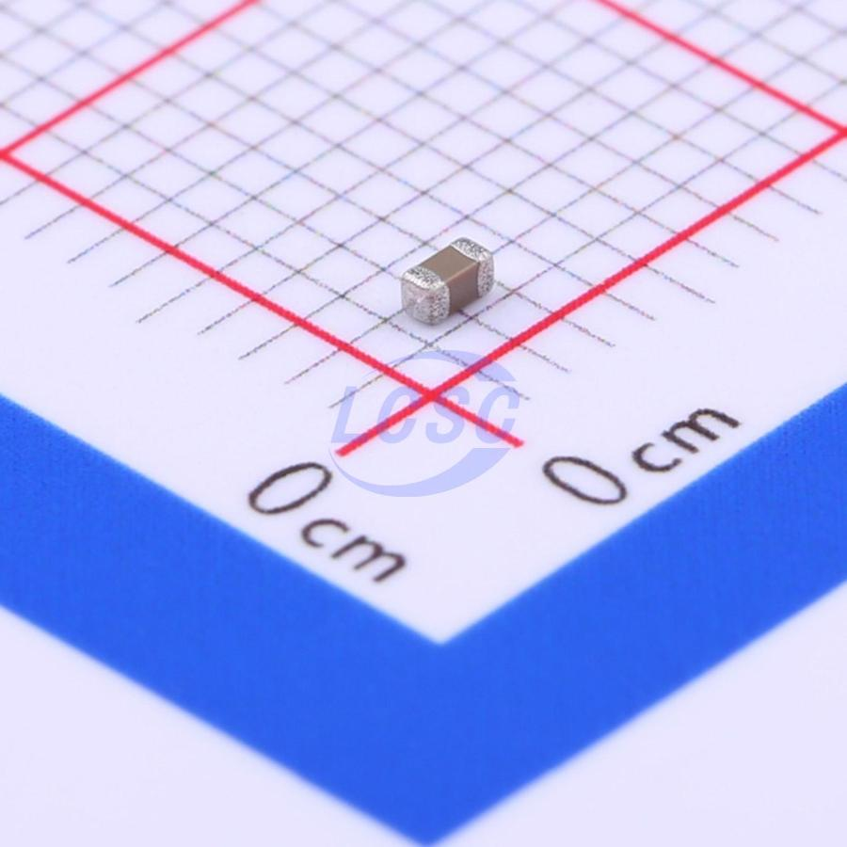
pcb/dossier/img/jlcpcb-part-photos/jlcpcb-placement-v07c-10.png
