jmcpheron/picowallet/pcb/dossier/img/jlcpcb-pcba-parameters-v07c.png

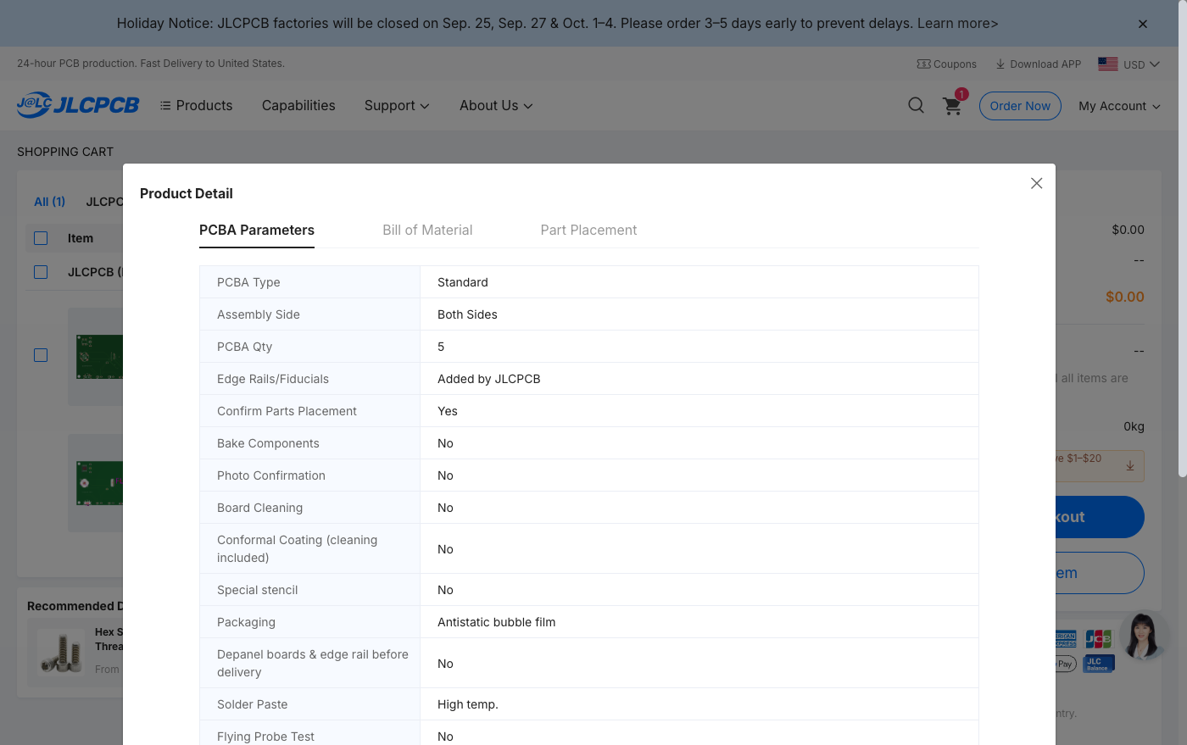
pcb/dossier/img/jlcpcb-pcba-parameters-v07c.png
