jmcpheron/picowallet/pcb/dossier/img/jlcpcb-placement-dialog-v07c.png

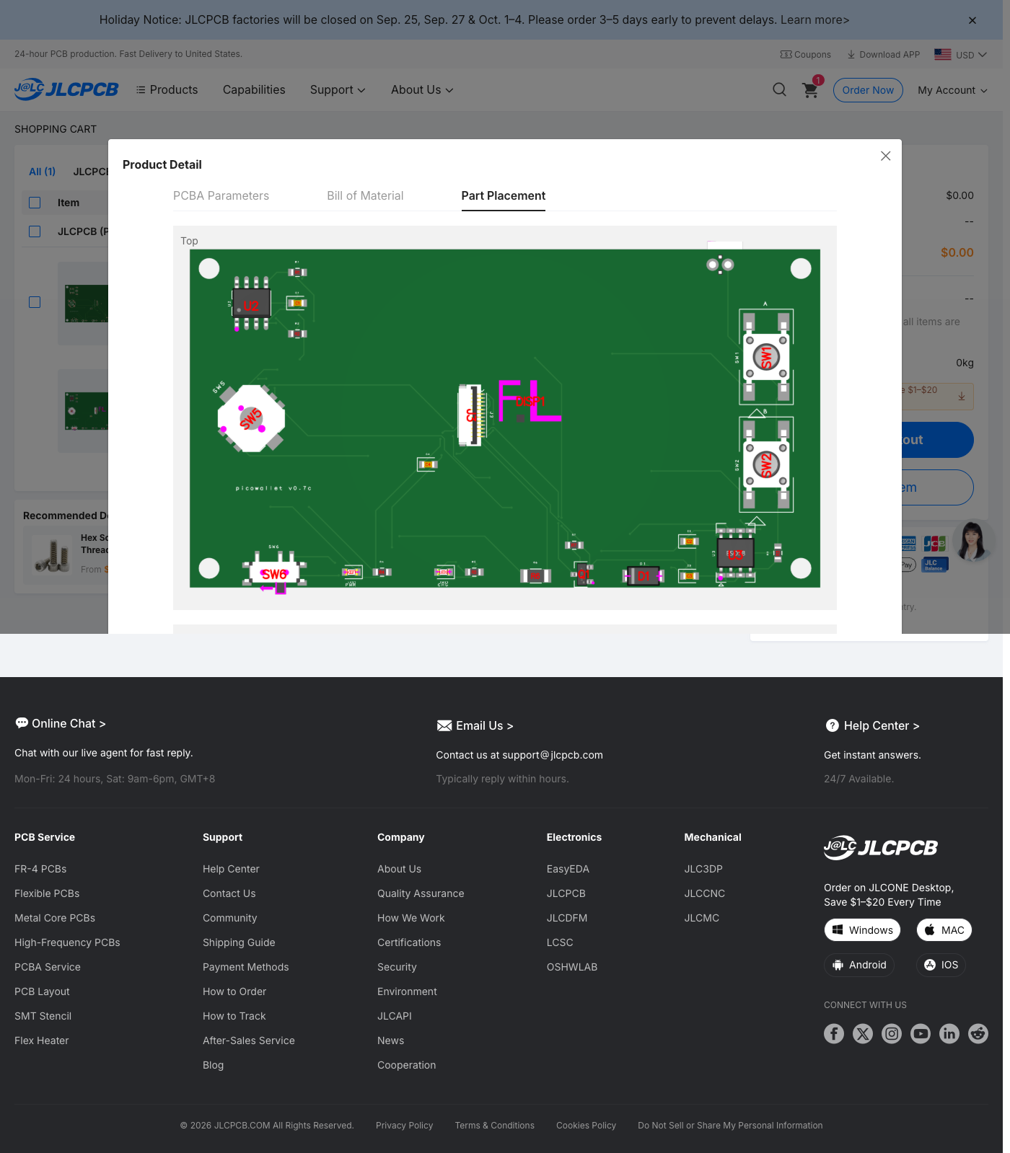
pcb/dossier/img/jlcpcb-placement-dialog-v07c.png
