jmcpheron/picowallet/pcb/dossier/img/jlcpcb-placement-v07c-bottom.png

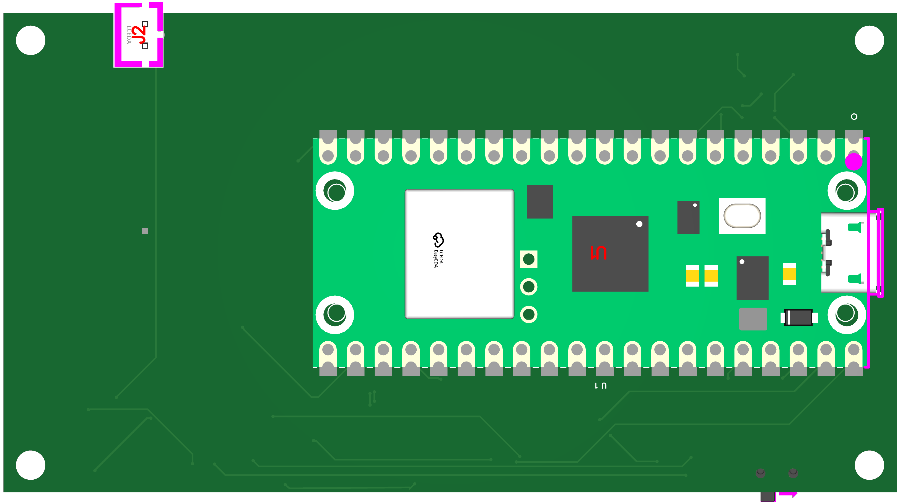
pcb/dossier/img/jlcpcb-placement-v07c-bottom.png
