jmcpheron/picowallet/pcb/dossier/img/jlcpcb-placement-v07c-top.png

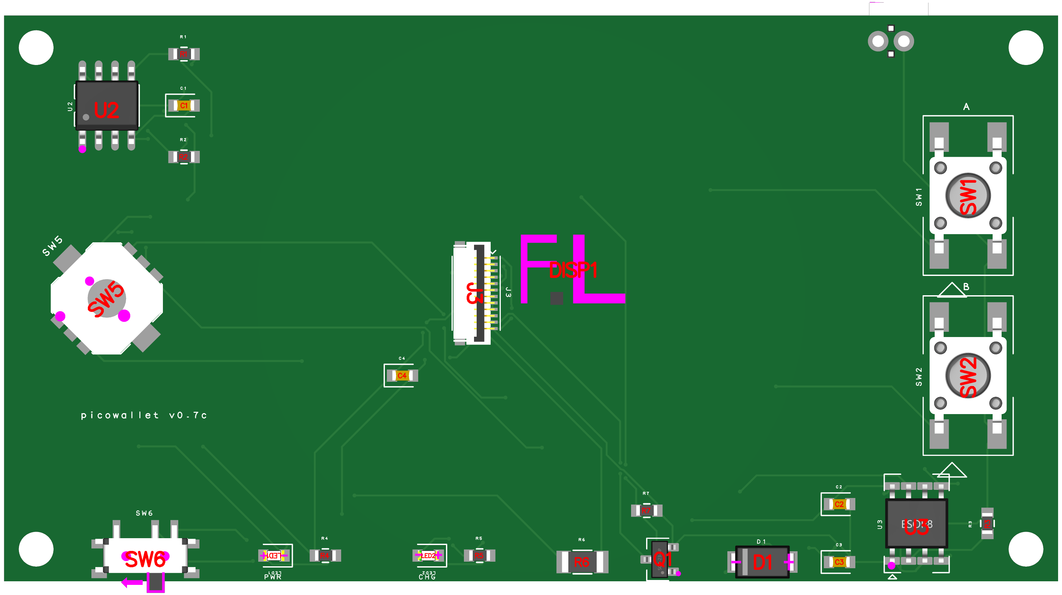
pcb/dossier/img/jlcpcb-placement-v07c-top.png
