jmcpheron/picowallet/pcb/dossier/img/jlcpcb-quote-v07.png

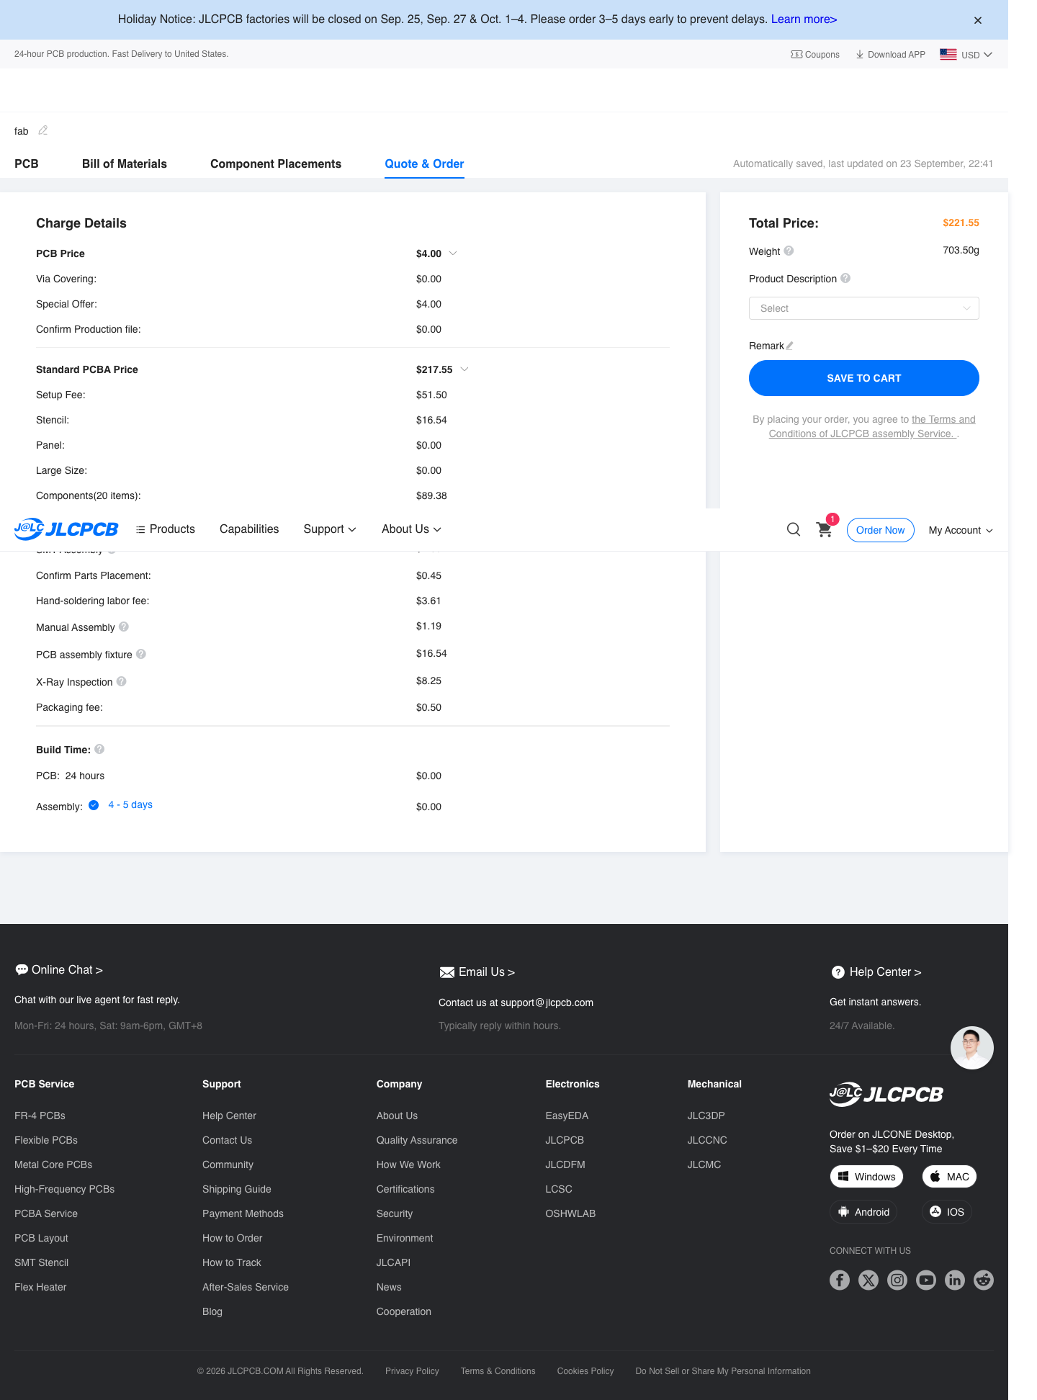
pcb/dossier/img/jlcpcb-quote-v07.png
