jmcpheron/picowallet/pcb/dossier/img/jlcpcb-top-placement-v07.png

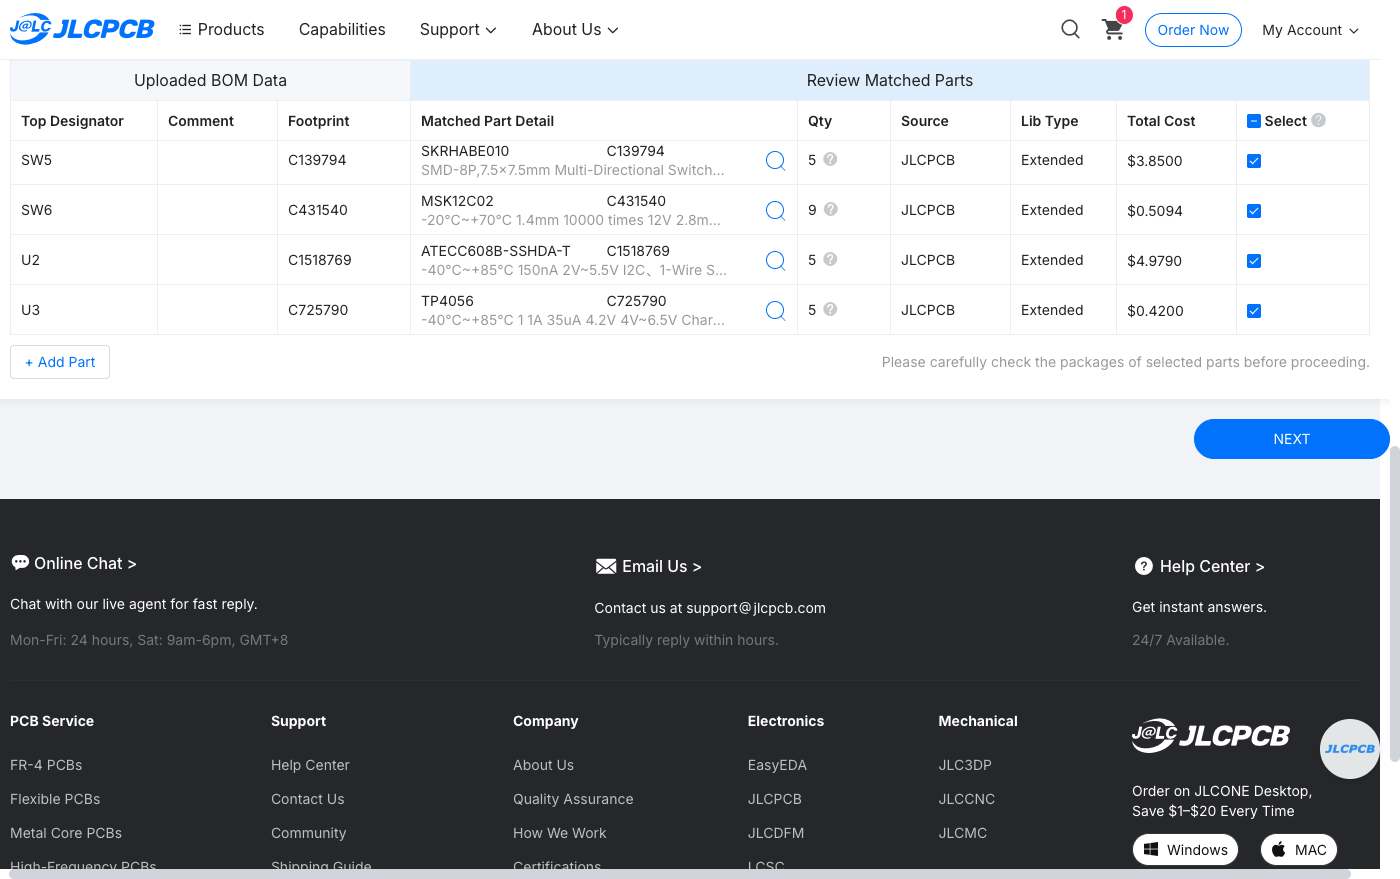
pcb/dossier/img/jlcpcb-top-placement-v07.png
