jmcpheron/picowallet/pcb/dossier/img/panel-back-lcsc.jpg

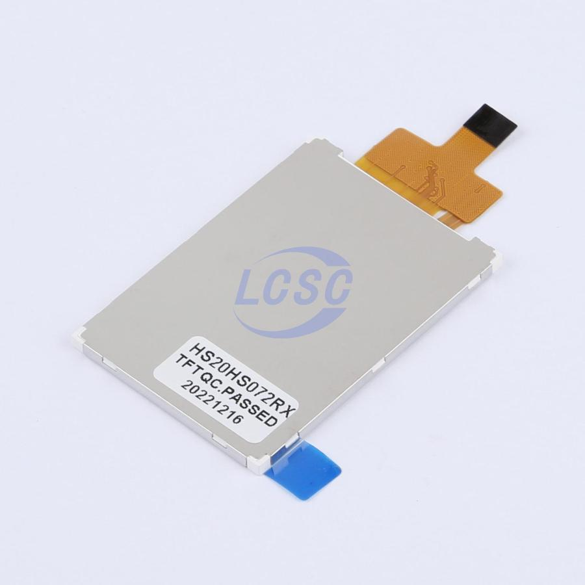
pcb/dossier/img/panel-back-lcsc.jpg
