jmcpheron/picowallet/pcb/dossier/img/panel-drawing-back-crop.png

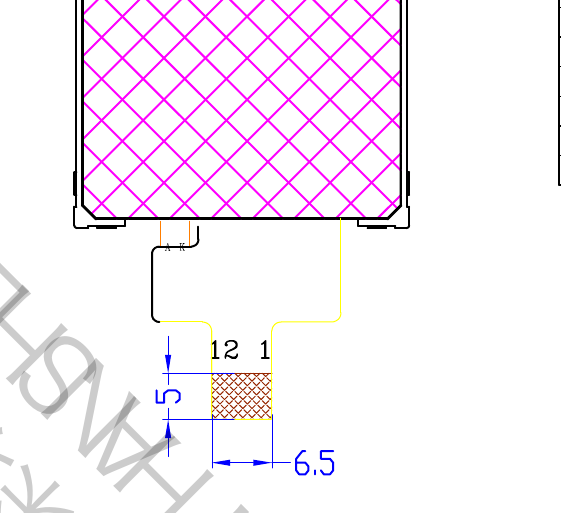
pcb/dossier/img/panel-drawing-back-crop.png
