jmcpheron/picowallet/pcb/dossier/img/panel-drawing-front-crop.png

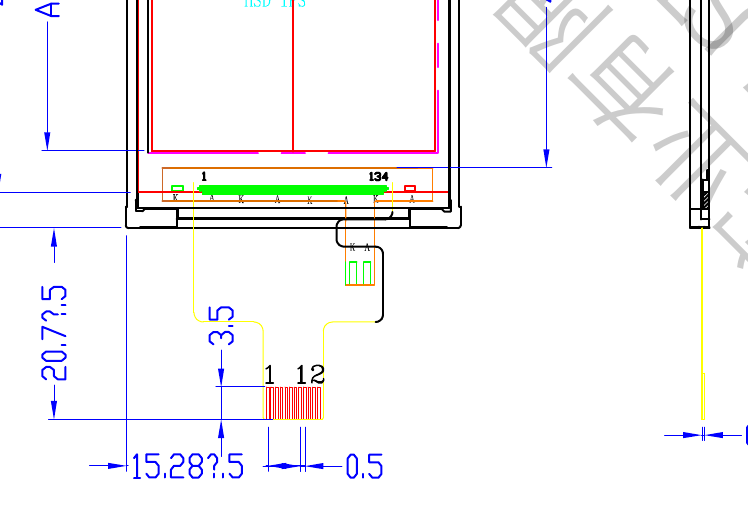
pcb/dossier/img/panel-drawing-front-crop.png
