jmcpheron/picowallet/pcb/dossier/img/panel-drawing-page10-upright.png

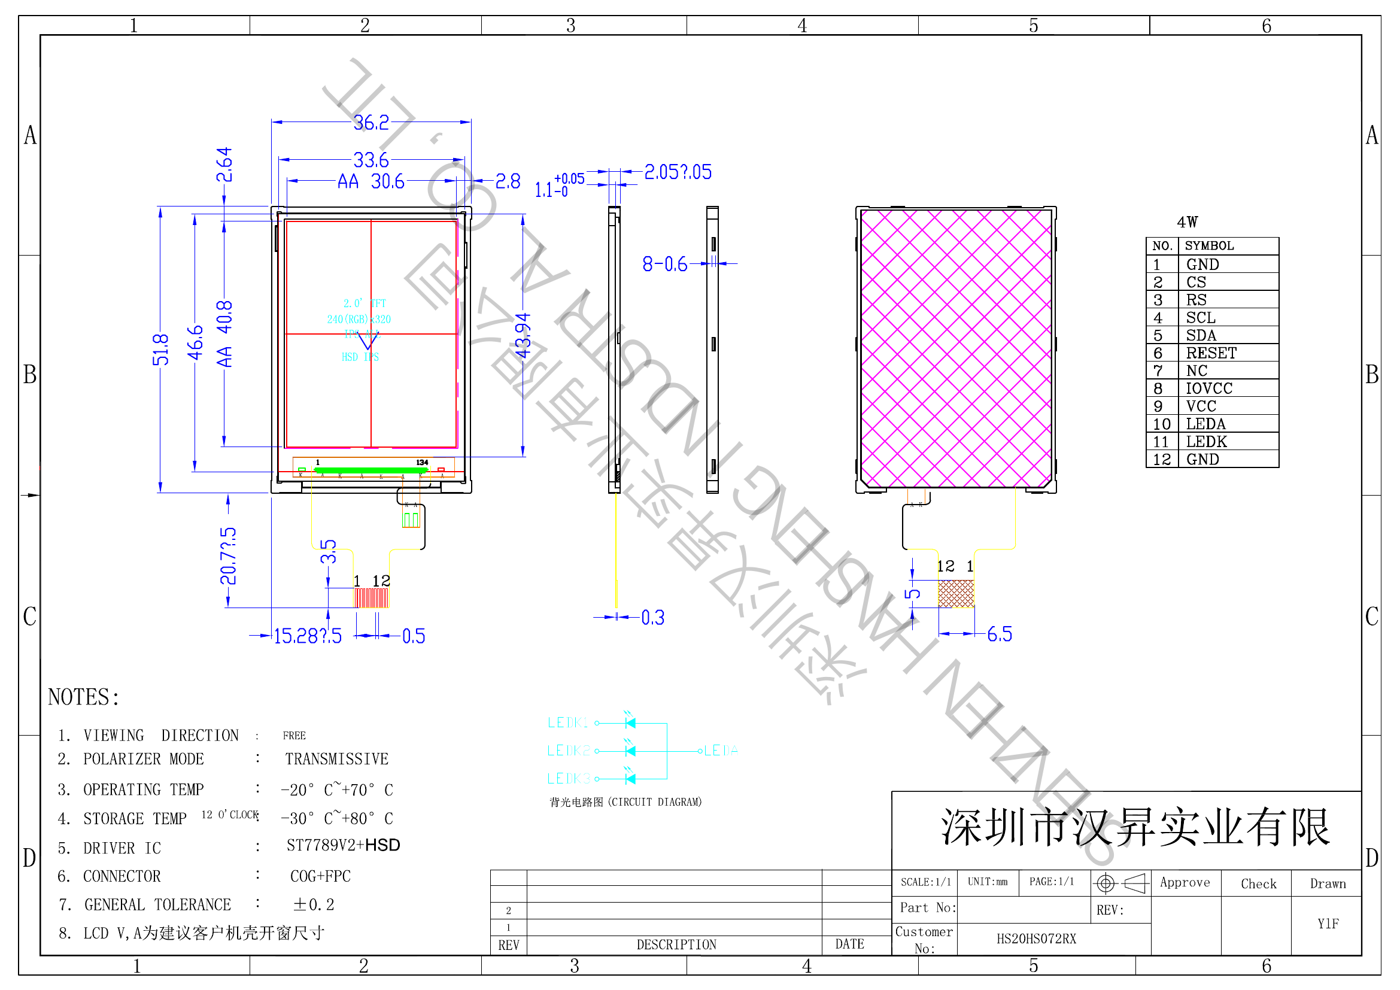
pcb/dossier/img/panel-drawing-page10-upright.png
