jmcpheron/picowallet/pcb/dossier/img/panel-drawing-pintable-crop.png

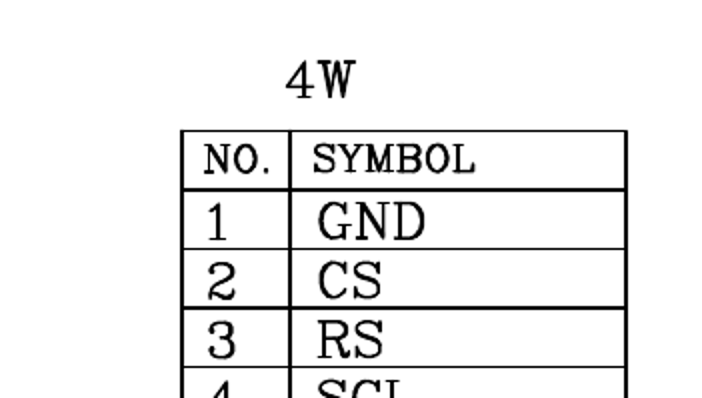
pcb/dossier/img/panel-drawing-pintable-crop.png
