jmcpheron/picowallet/pcb/dossier/review/AFC42-drawing.png

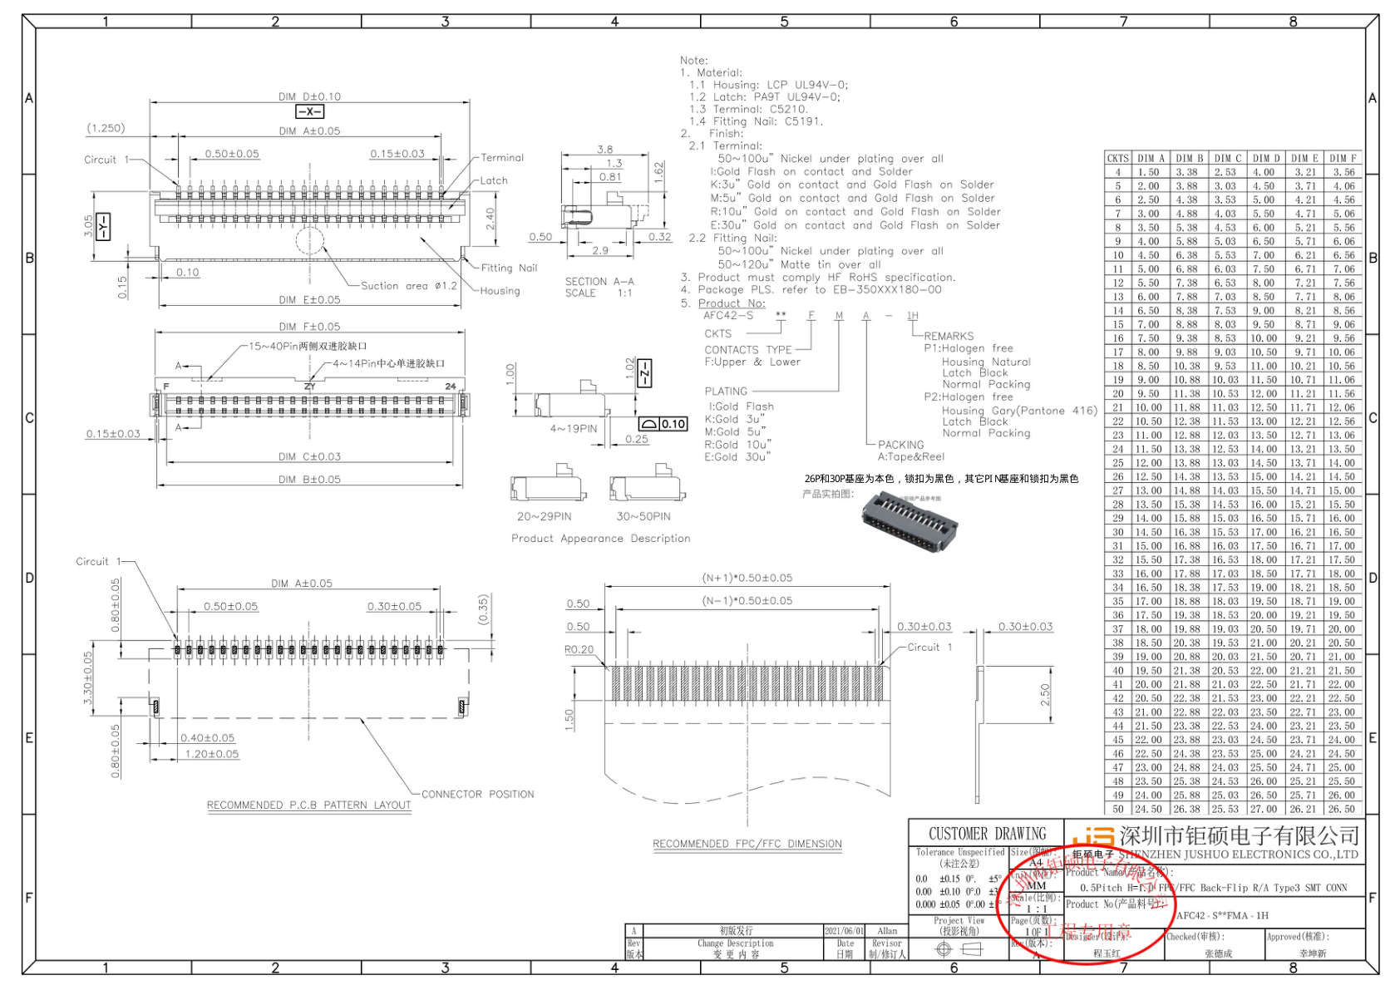
pcb/dossier/review/AFC42-drawing.png
