jmcpheron/picowallet/pcb/dossier/review/MSK12C02-drawing.png

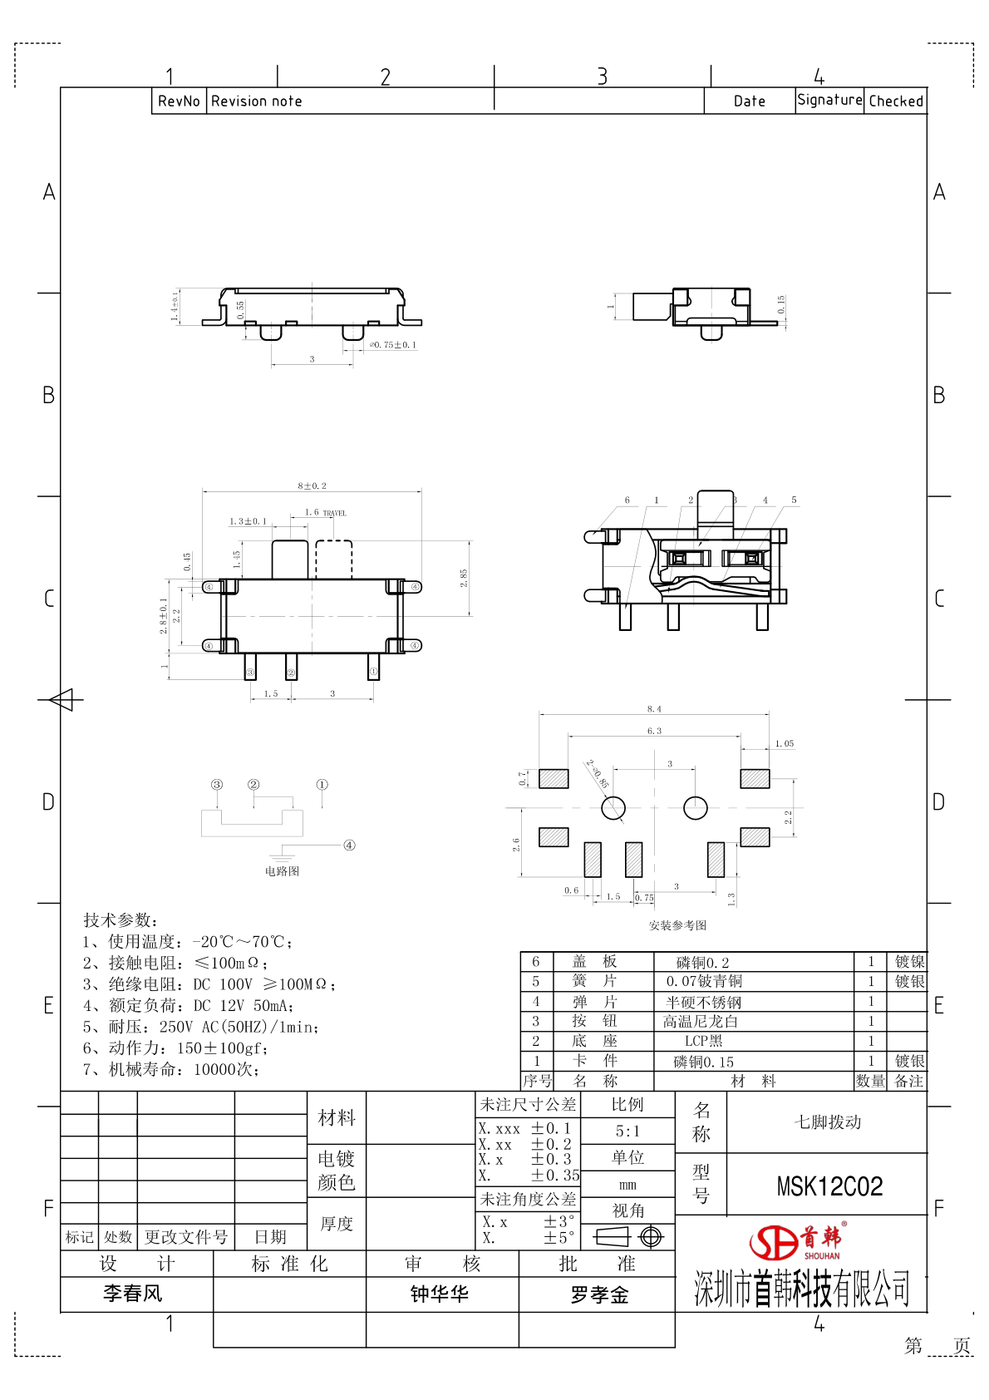
pcb/dossier/review/MSK12C02-drawing.png
