jmcpheron/picowallet/pcb/usb-signer/ref/usb-c-plug-photo.jpg

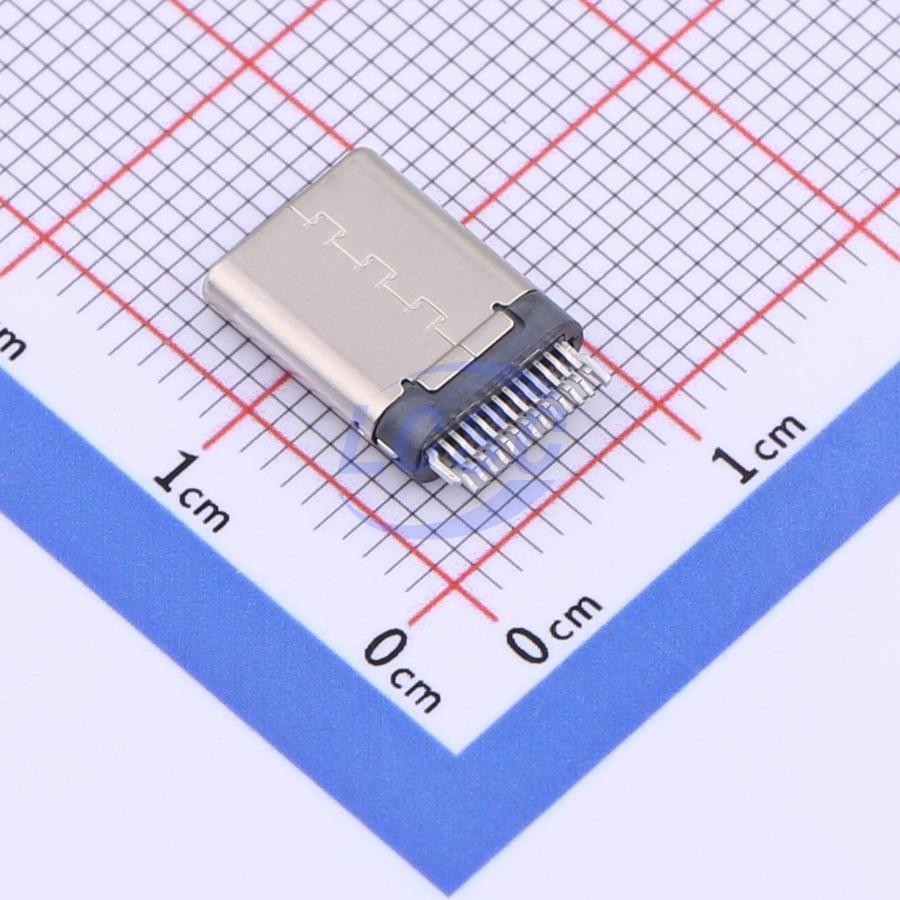
pcb/usb-signer/ref/usb-c-plug-photo.jpg
