jmcpheron/picowallet/pcb/usb-signer/render/3d-angle.png

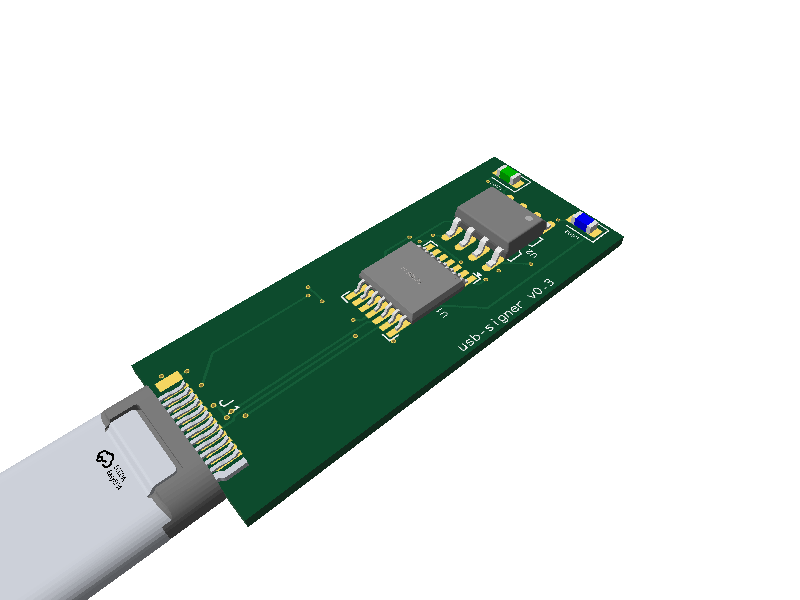
pcb/usb-signer/render/3d-angle.png
