jmcpheron/picowallet/pcb/usb-signer/render/3d-top.png

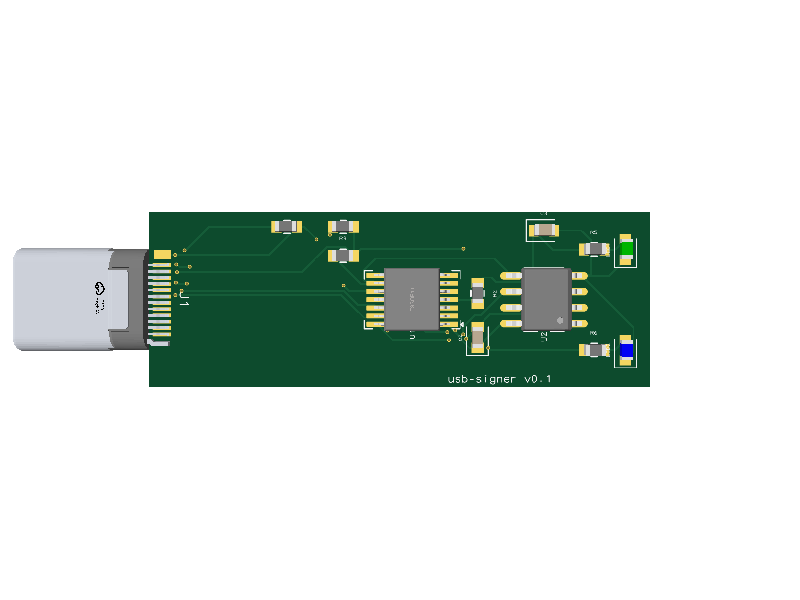
pcb/usb-signer/render/3d-top.png
