jmcpheron/picowallet/pcb/usb-signer/render/pcb.png

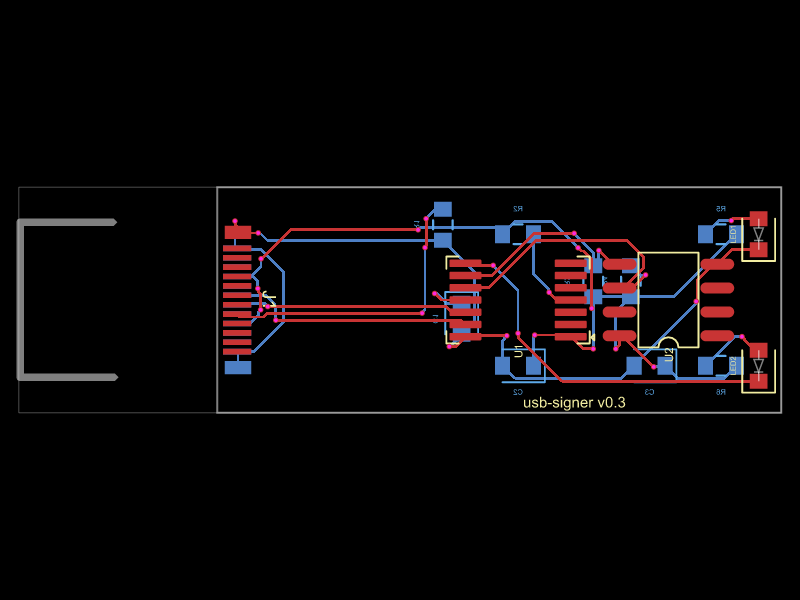
pcb/usb-signer/render/pcb.png
