jmcpheron/picowallet/pcb/v0/render/3d-top.png

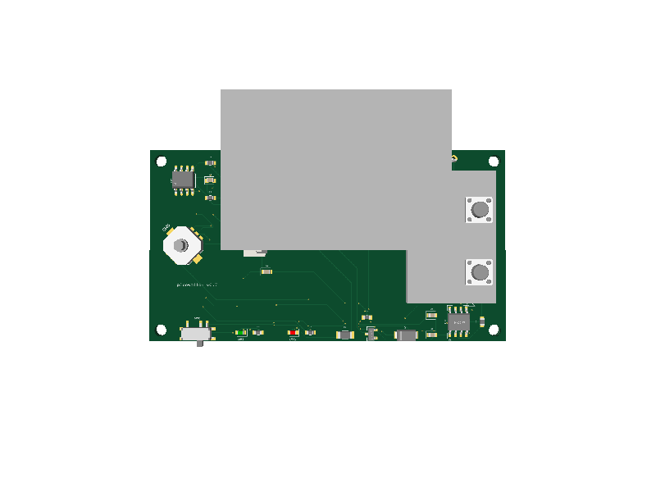
pcb/v0/render/3d-top.png
