jmcpheron/picowallet/pcb/v0/render/jlcpcb-checkout.png

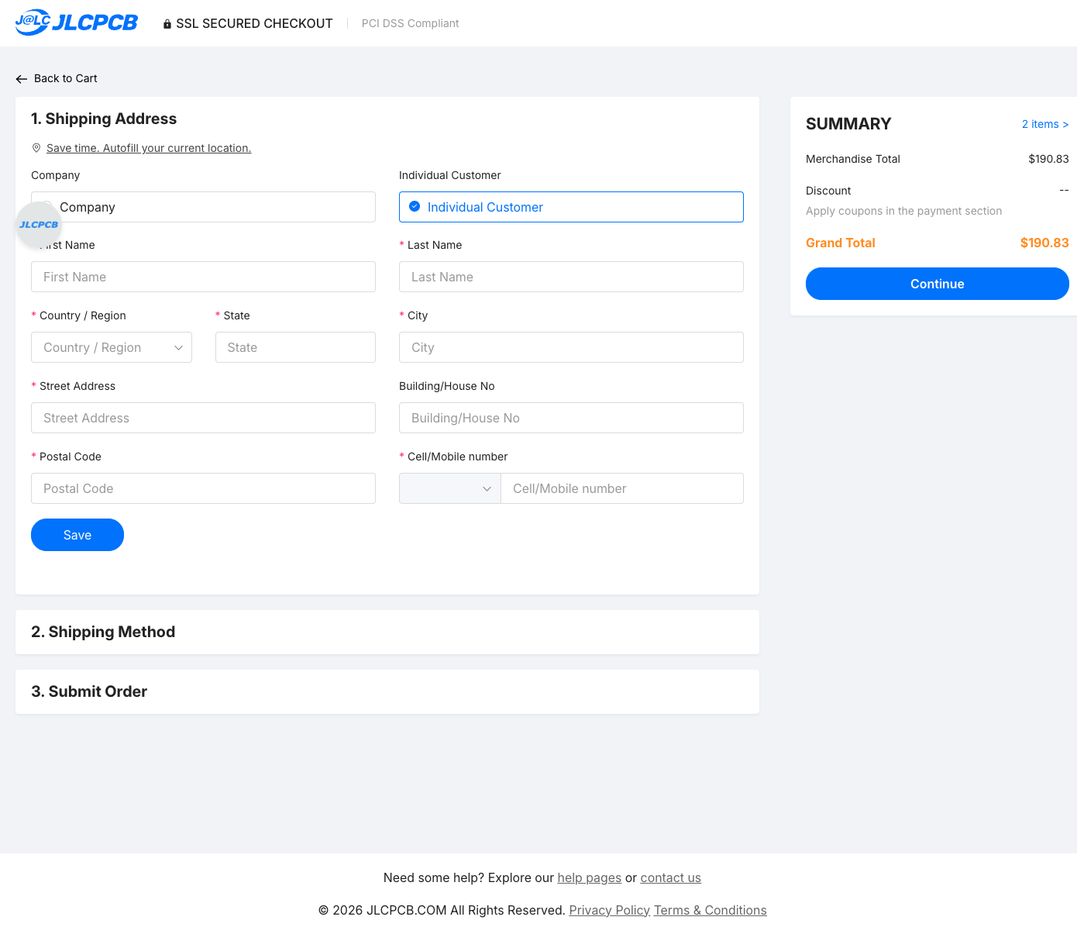
pcb/v0/render/jlcpcb-checkout.png
