jmcpheron/picowallet/pcb/v0/render/switch-closeup.png

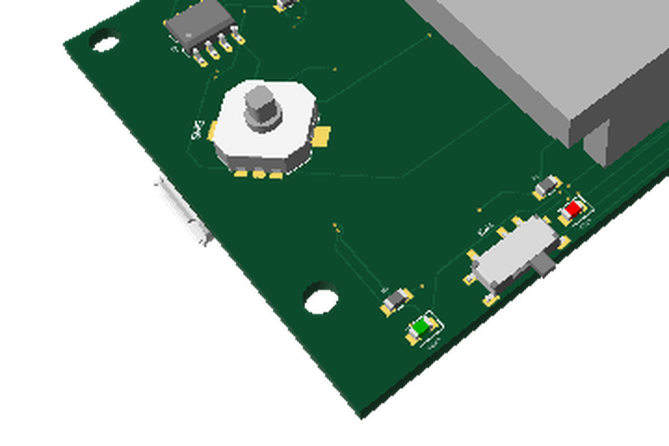
pcb/v0/render/switch-closeup.png
