jmcpheron/picowallet/case/out/v06_lid.stl

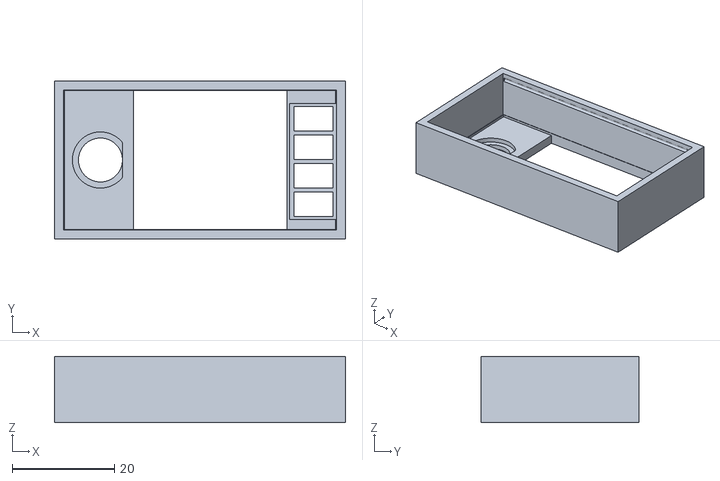
[picture p75: CAD file, 2026-09-07]
case/out/v06_lid.stl
57.0 x 31.0 x 13.0
