jmcpheron/picowallet/case/zez0000/base_v5_qr_black.stl

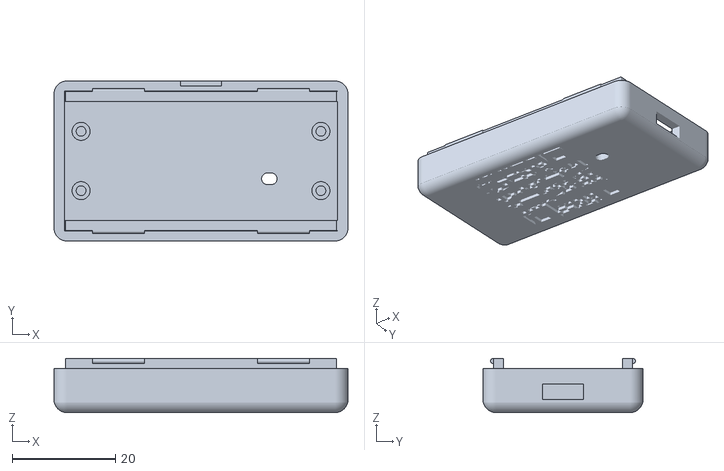
[picture p76: CAD file, 2026-09-11]
case/zez0000/base_v5_qr_black.stl
57.0 x 31.0 x 10.5
