jmcpheron/picowallet/reference/seedsigner/open_pill_mini_w_coverplate_Thumbstick_PLA.stl

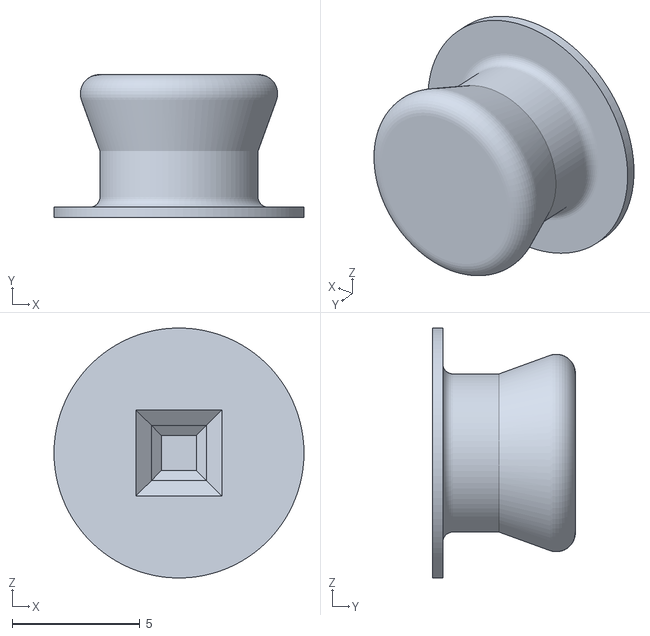
[picture p77: CAD file, 2026-09-06]
reference/seedsigner/open_pill_mini_w_coverplate_Thumbstick_PLA.stl
9.80 x 5.60 x 9.79
