jmcpheron/picowallet/case/out/v06b_caps_hat_plate.stl

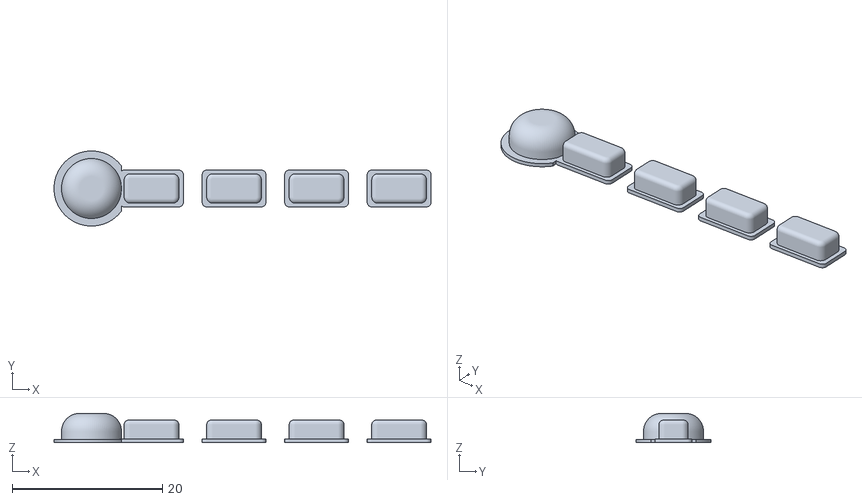
[picture p78: CAD file, 2026-09-07]
case/out/v06b_caps_hat_plate.stl
50.2 x 10.00 x 3.90
