jmcpheron/picowallet/case/zez0000/base_v5_qr_white.stl

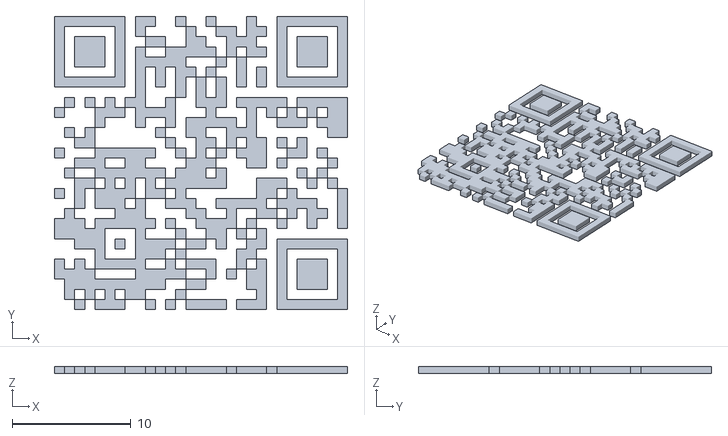
[picture p79: CAD file, 2026-09-11]
case/zez0000/base_v5_qr_white.stl
24.6 x 24.6 x 0.6
