jmcpheron/picowallet/case/out/v0_keycaps_test_plate.stl

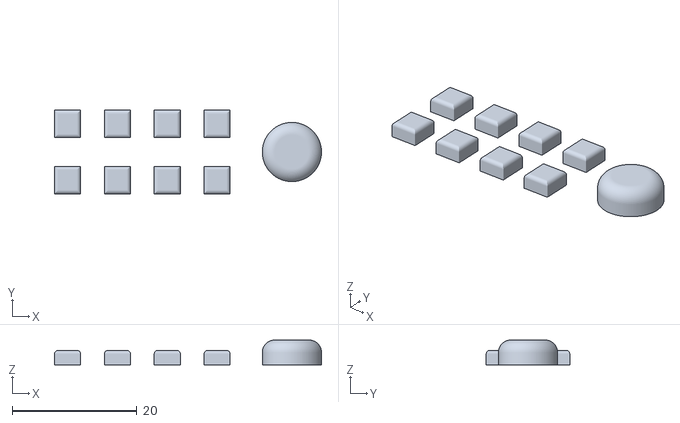
[picture p80: CAD file, 2026-09-06]
case/out/v0_keycaps_test_plate.stl
42.8 x 13.4 x 4.00
