jmcpheron/picowallet/case/zez0000/base_v5_qr.3mf

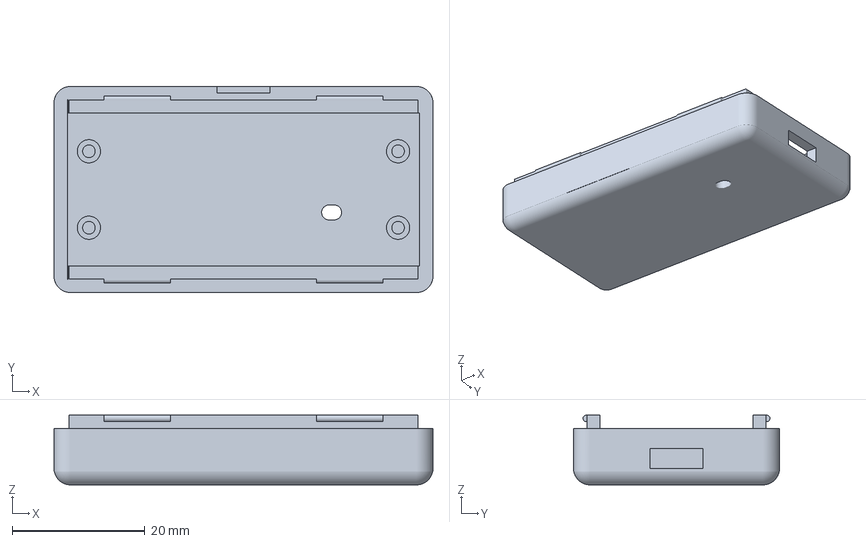
[picture p81: CAD file, 2026-09-11]
case/zez0000/base_v5_qr.3mf
57.0 x 31.0 x 10.5 mm
