jmcpheron/picowallet/case/out/joystick_dome.stl

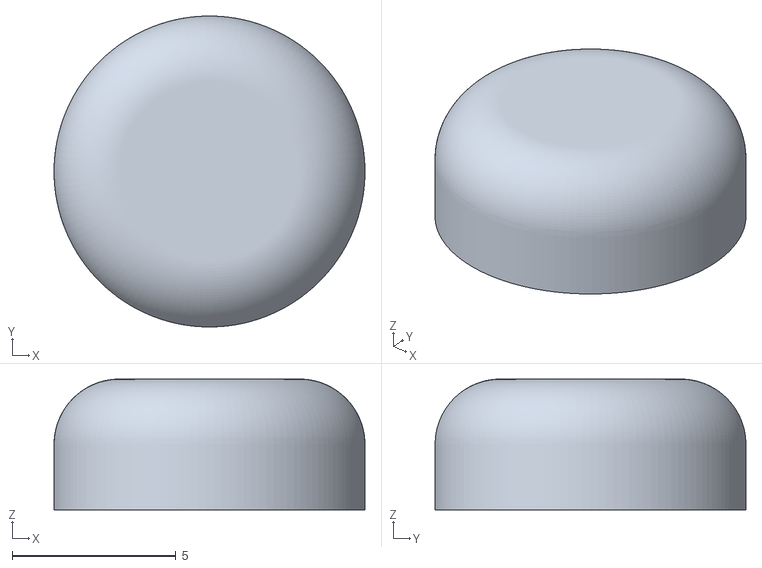
[picture p82: CAD file, 2026-09-06]
case/out/joystick_dome.stl
9.50 x 9.50 x 4.00
