jmcpheron/picowallet/case/out/keycaps_x4_pocket2.05.stl

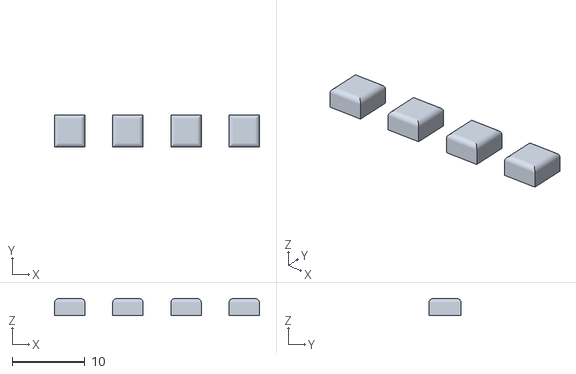
[picture p83: CAD file, 2026-09-06]
case/out/keycaps_x4_pocket2.05.stl
28.2 x 4.42 x 2.35
