jmcpheron/picowallet/case/out/v1_floating_caps_x4_clear0.15.stl

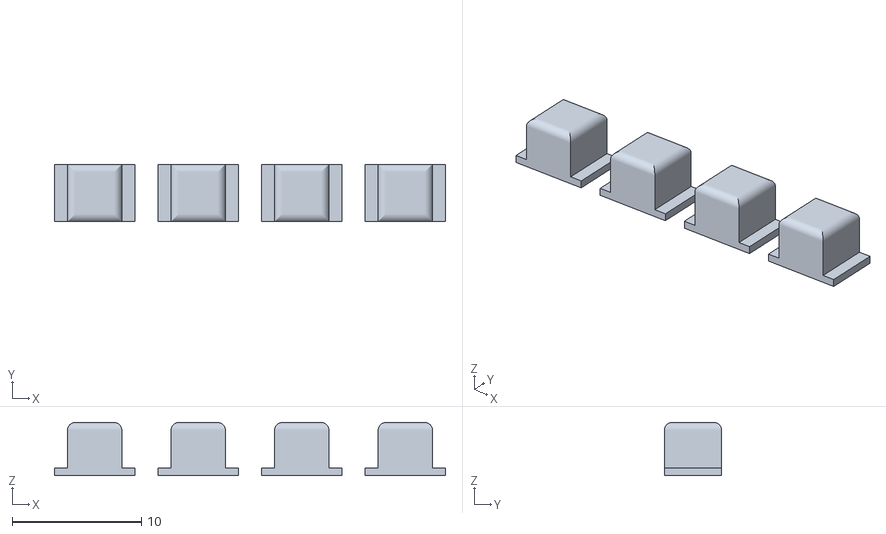
[picture p84: CAD file, 2026-09-06]
case/out/v1_floating_caps_x4_clear0.15.stl
30.2 x 4.42 x 4.10
