jmcpheron/picowallet/case/out/v1_floating_caps_x4_clear0.25.stl

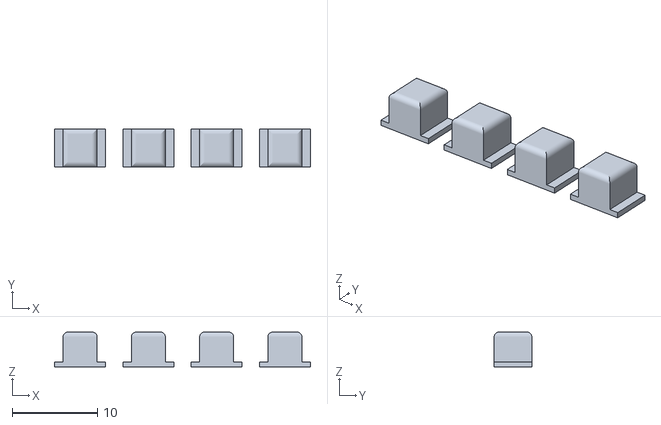
[picture p85: CAD file, 2026-09-06]
case/out/v1_floating_caps_x4_clear0.25.stl
30.0 x 4.42 x 4.10
