jmcpheron/picowallet/case/zez0000/button_cap_x.stl

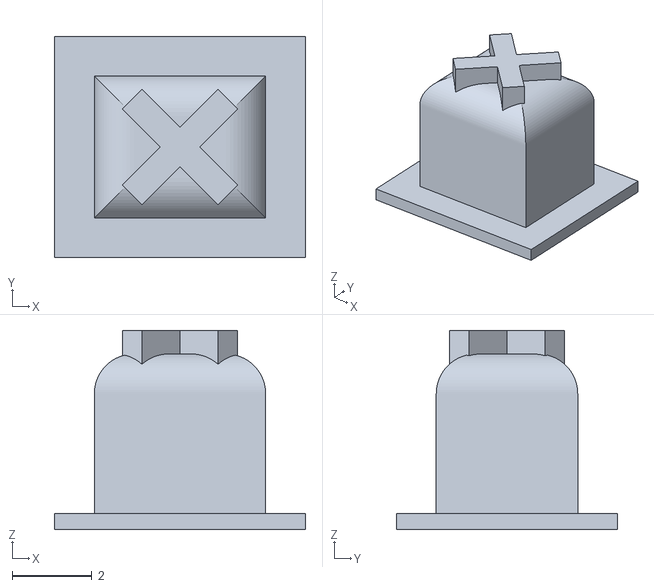
[picture p86: CAD file, 2026-09-11]
case/zez0000/button_cap_x.stl
6.30 x 5.56 x 5.00
