jmcpheron/picowallet/case/zez0000/joystick_cap_v3_2.15.stl

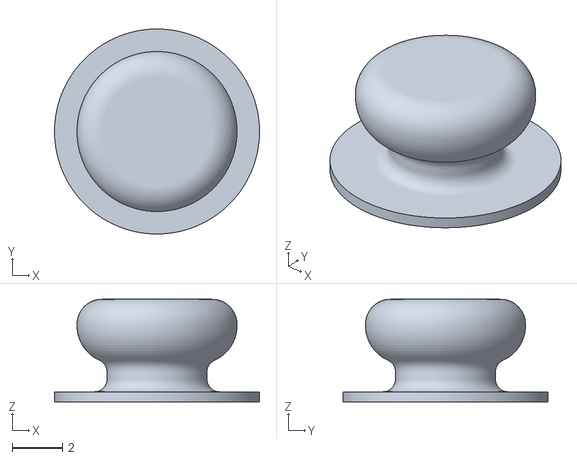
[picture p87: CAD file, 2026-09-11]
case/zez0000/joystick_cap_v3_2.15.stl
8.20 x 8.20 x 4.10
