jmcpheron/picowallet/case/zez0000/button_cap_2.stl

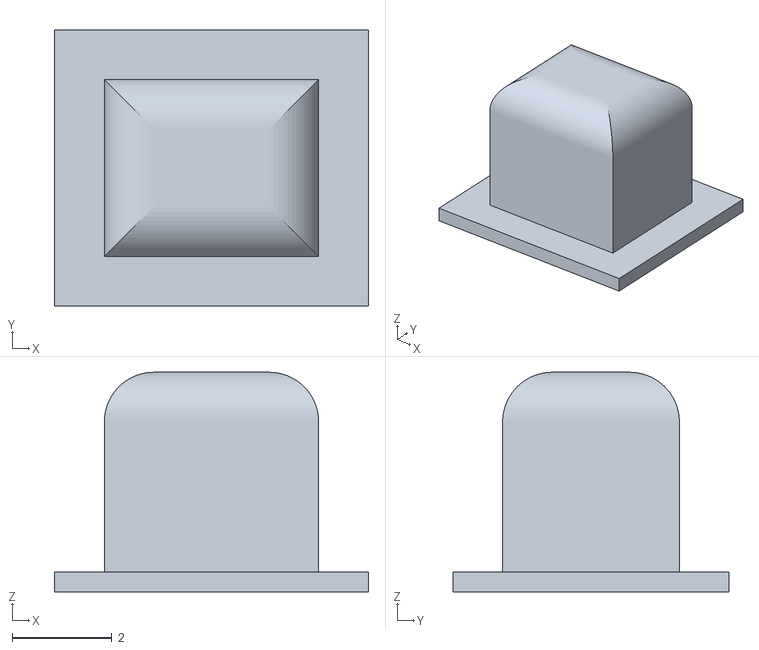
[picture p88: CAD file, 2026-09-09]
case/zez0000/button_cap_2.stl
6.30 x 5.55 x 4.41
