jmcpheron/picowallet/case/zez0000/button_cap_4.stl

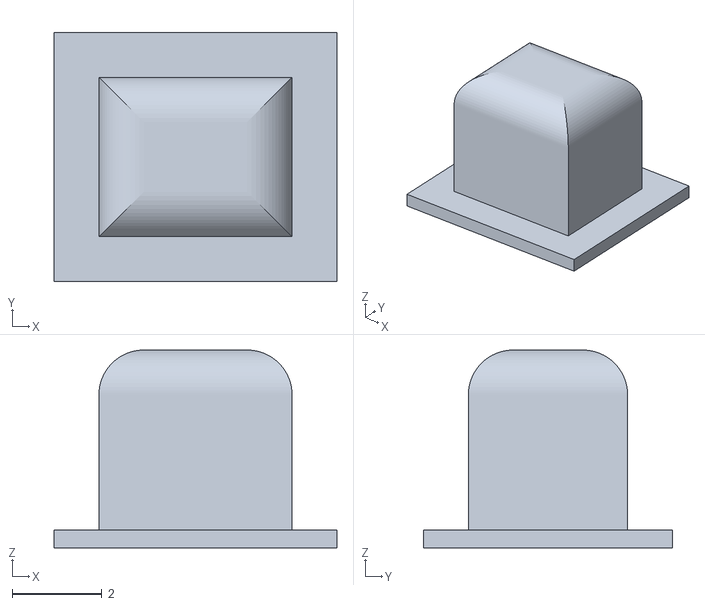
[picture p89: CAD file, 2026-09-09]
case/zez0000/button_cap_4.stl
6.30 x 5.55 x 4.41
