jmcpheron/picowallet/buildlog/images/2026-09-05-12-caliper-30.94-case-width.jpg

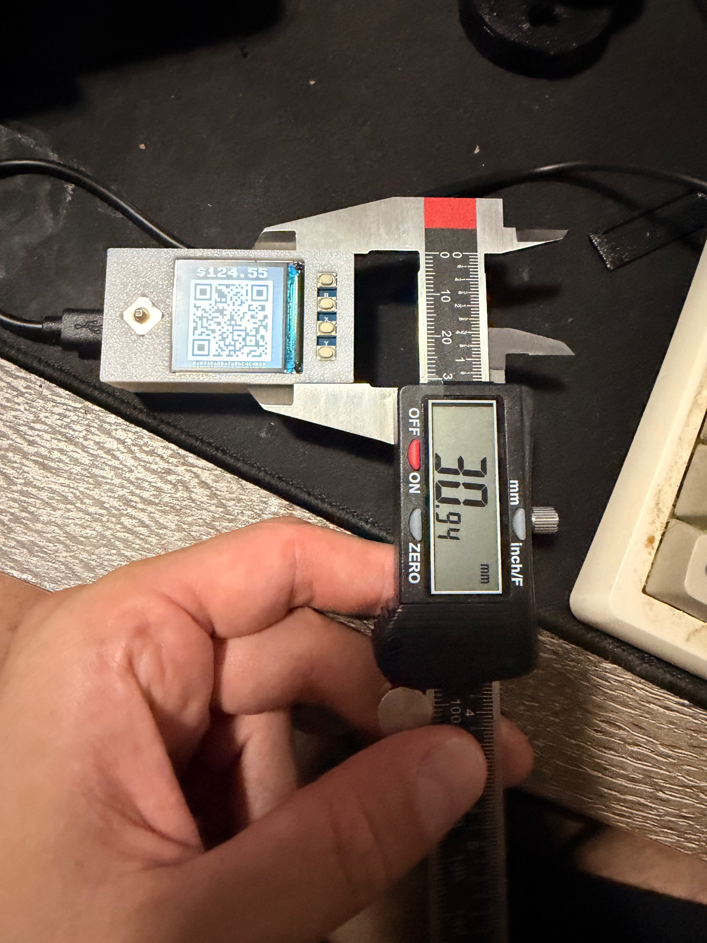
buildlog/images/2026-09-05-12-caliper-30.94-case-width.jpg
